slash4you/Anemometre-Girouette/images/Anemometre Electronic v15.png

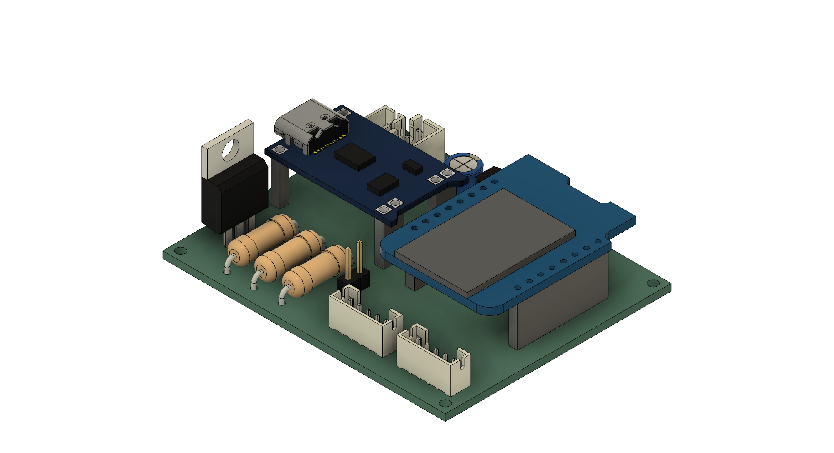
images/Anemometre Electronic v15.png
