slash4you/Anemometre-Girouette/images/Anemometre+Girouette v337.png

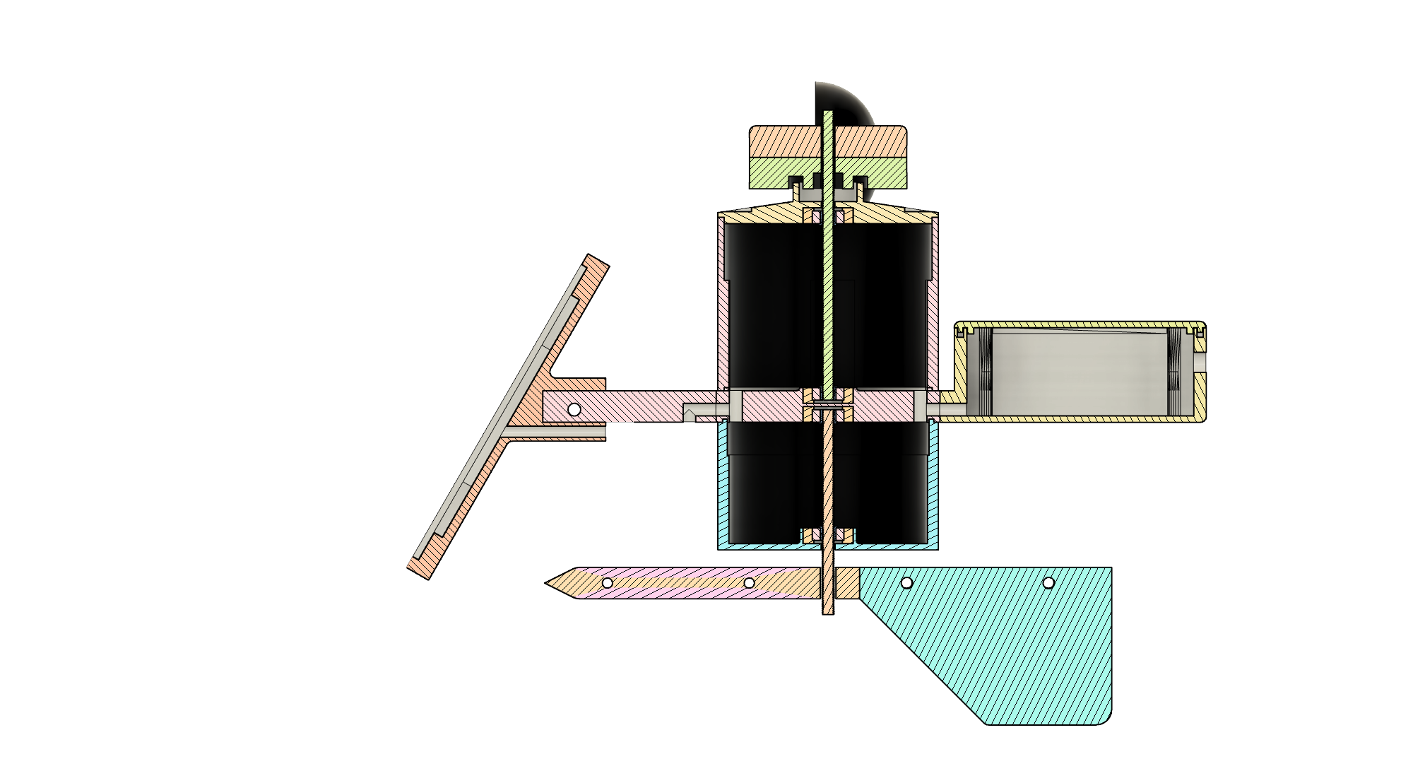
images/Anemometre+Girouette v337.png
