slash4you/Anemometre-Girouette/images/Anemometre+Girouette v337_2.png

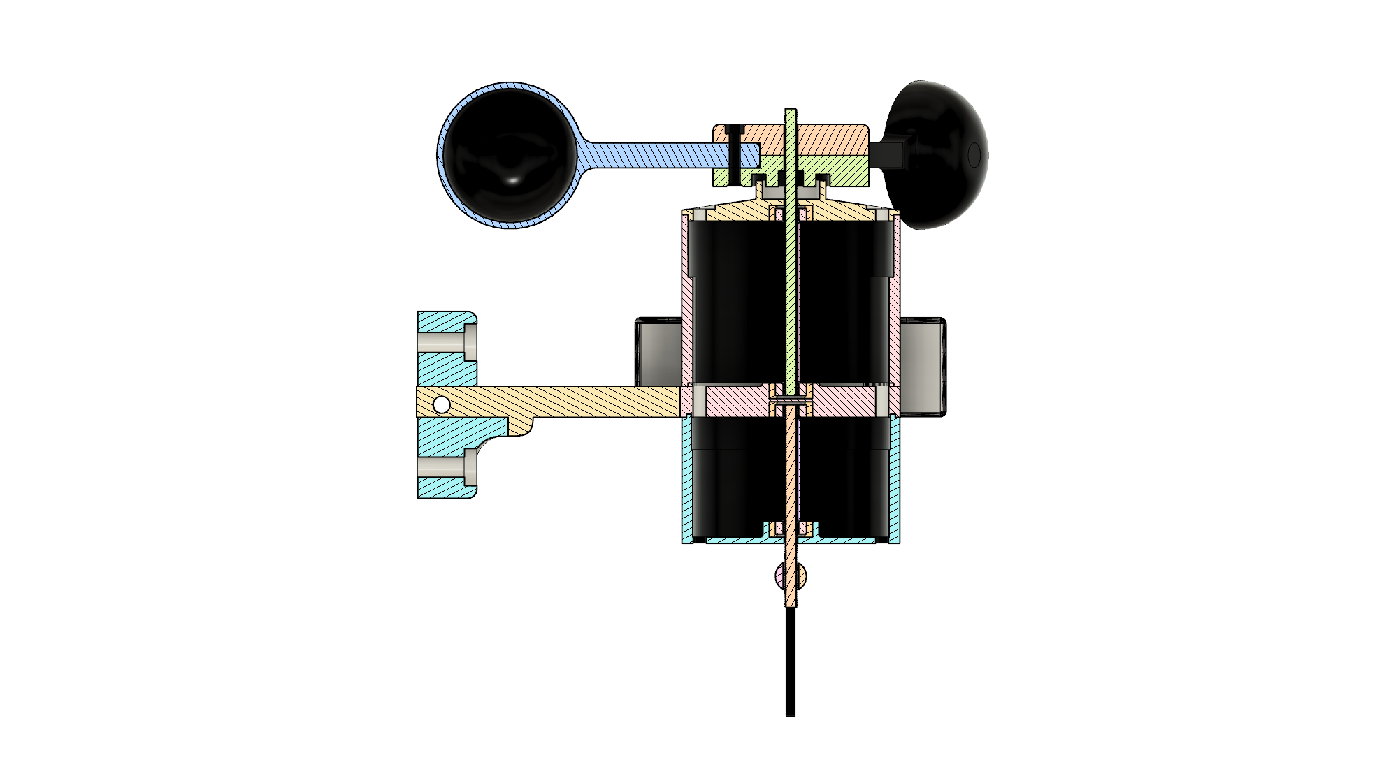
images/Anemometre+Girouette v337_2.png
