slash4you/Anemometre-Girouette/images/Anemometre+Girouette v337_3.png

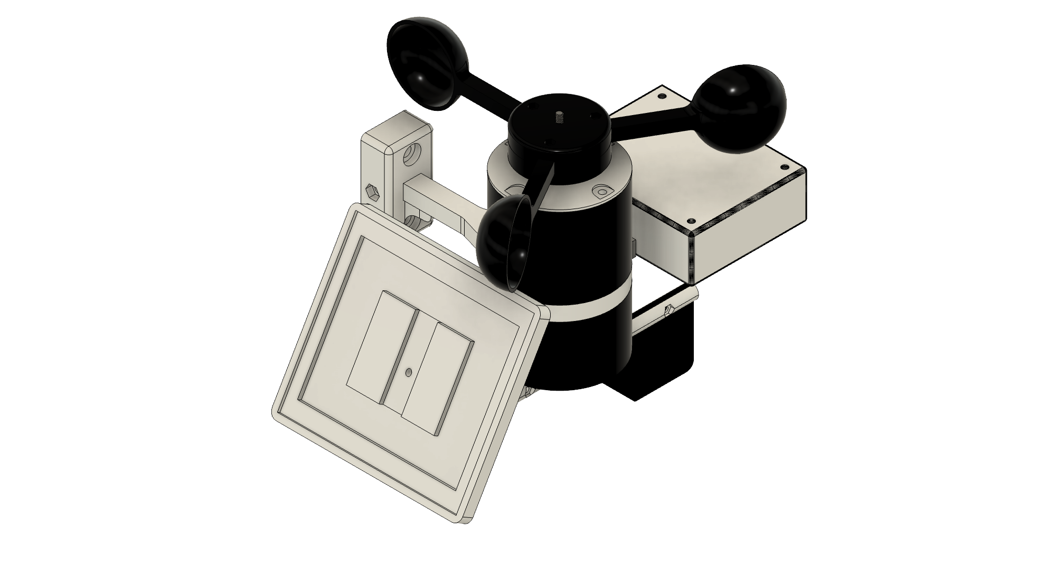
images/Anemometre+Girouette v337_3.png
