slash4you/Anemometre-Girouette/images/Anemometre+Girouette v337_4.png

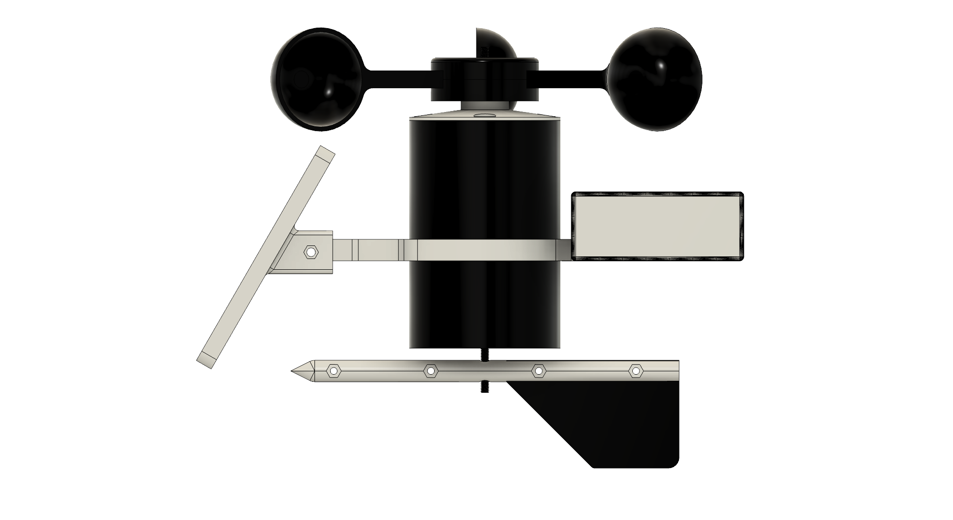
images/Anemometre+Girouette v337_4.png
