slash4you/Anemometre-Girouette/images/Anemometre+Girouette v337_5.png

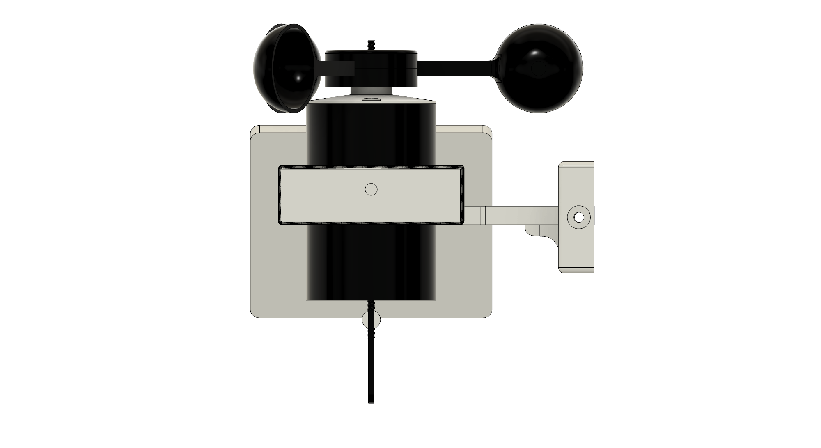
images/Anemometre+Girouette v337_5.png
