slash4you/Anemometre-Girouette/images/Anemometre+Girouette v337_6.png

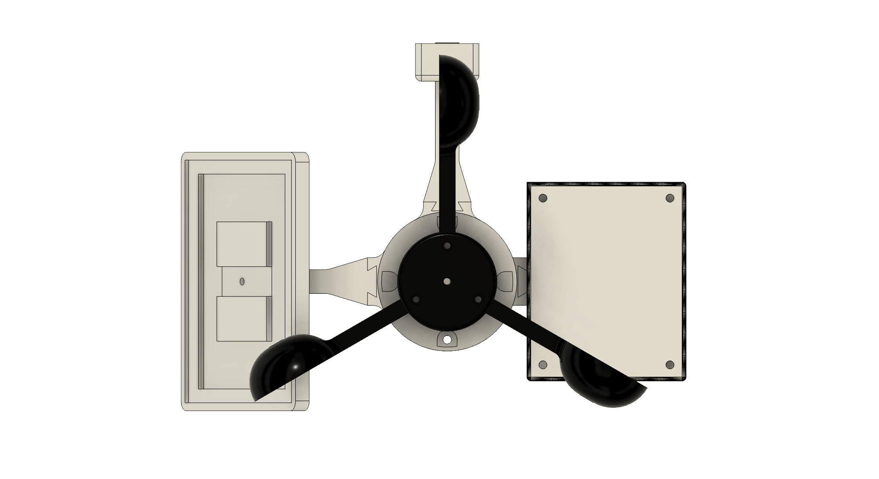
images/Anemometre+Girouette v337_6.png
