slash4you/Anemometre-Girouette/images/Anemometre+Girouette v343.png

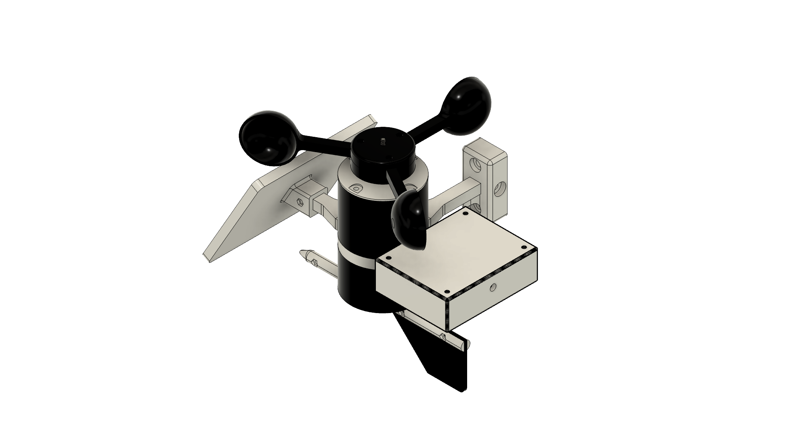
images/Anemometre+Girouette v343.png
