slash4you/Anemometre-Girouette/images/Anemometre+Girouette v345.png

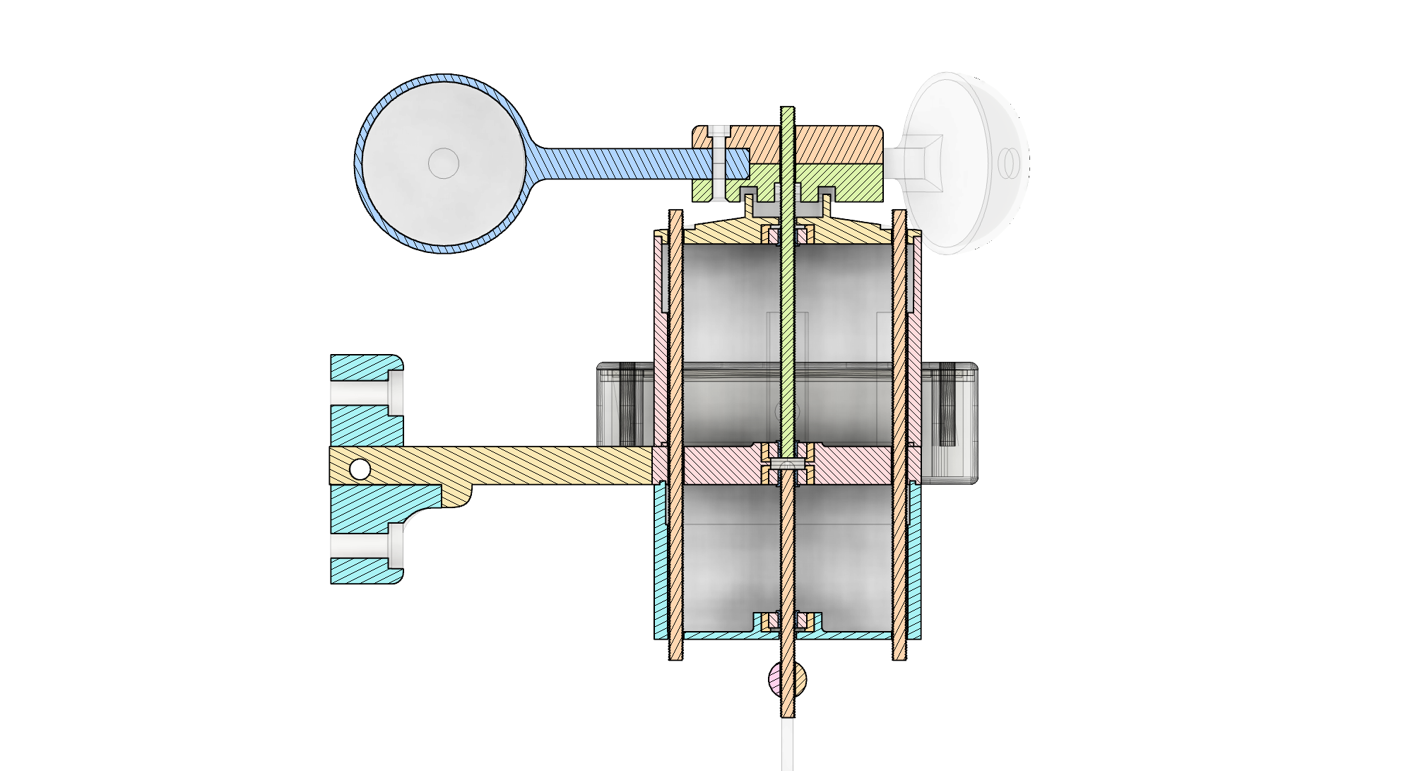
images/Anemometre+Girouette v345.png
