slash4you/Anemometre-Girouette/images/Anemometre+Girouette v345_2.png

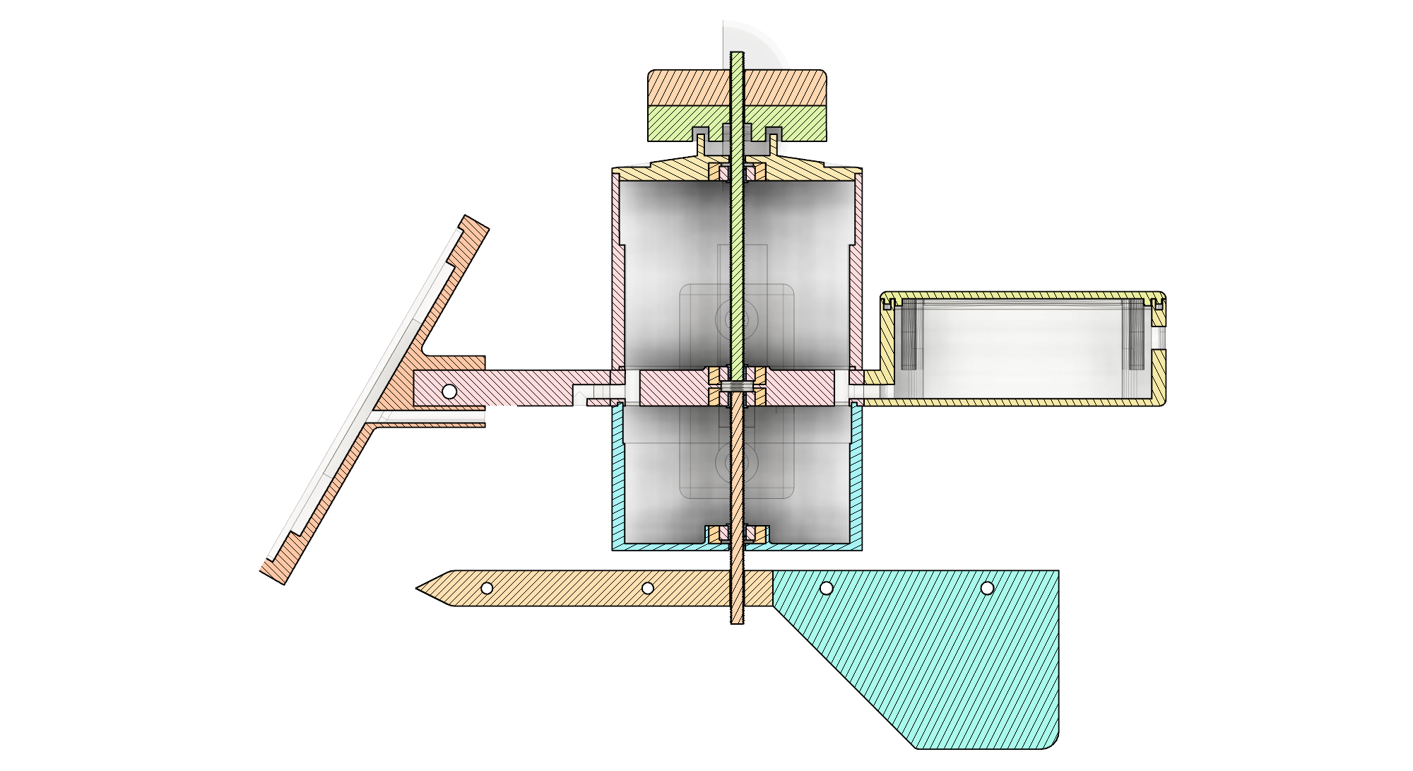
images/Anemometre+Girouette v345_2.png
