slash4you/Anemometre-Girouette/images/Anemometre+Girouette v345_3.png

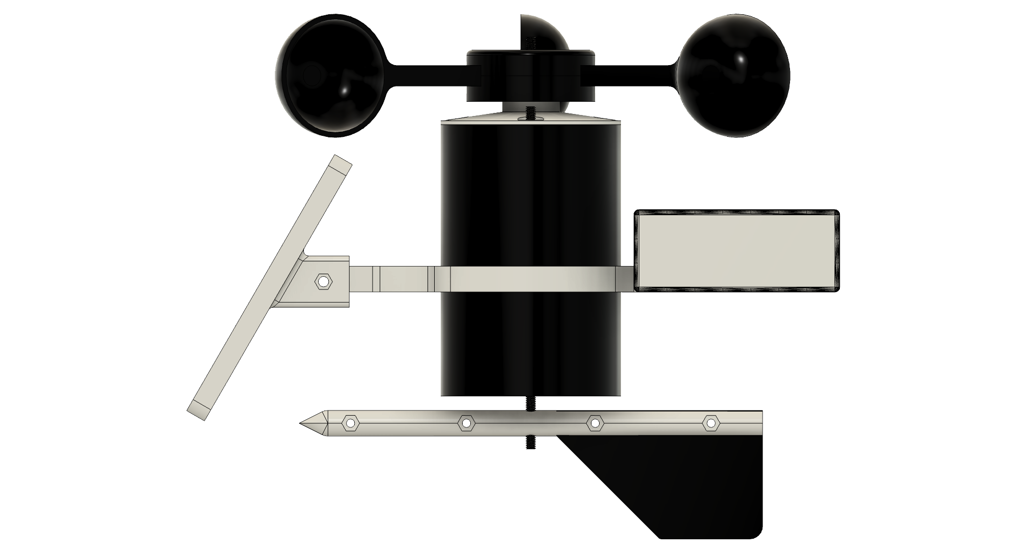
images/Anemometre+Girouette v345_3.png
