slash4you/Anemometre-Girouette/images/Anemometre+Girouette v345_5.png

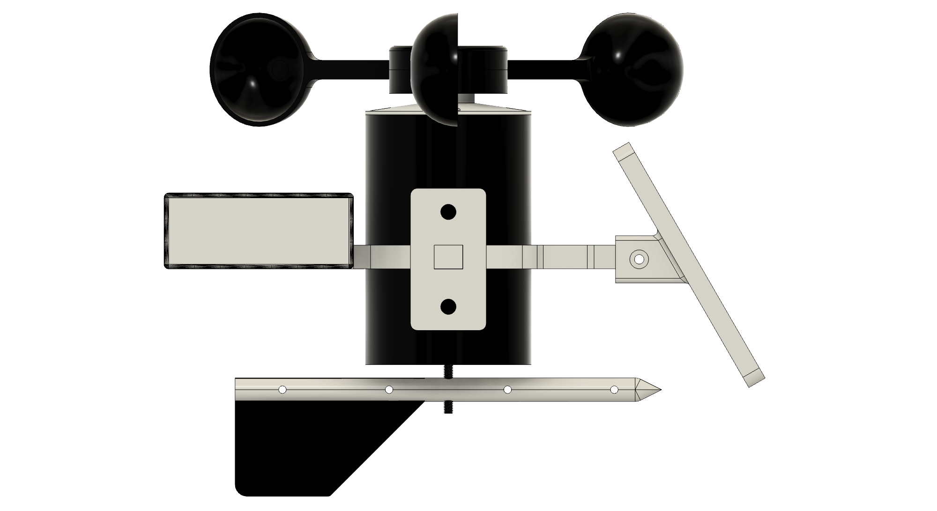
images/Anemometre+Girouette v345_5.png
