slash4you/Anemometre-Girouette/images/Anemometre+Girouette v345_6.png

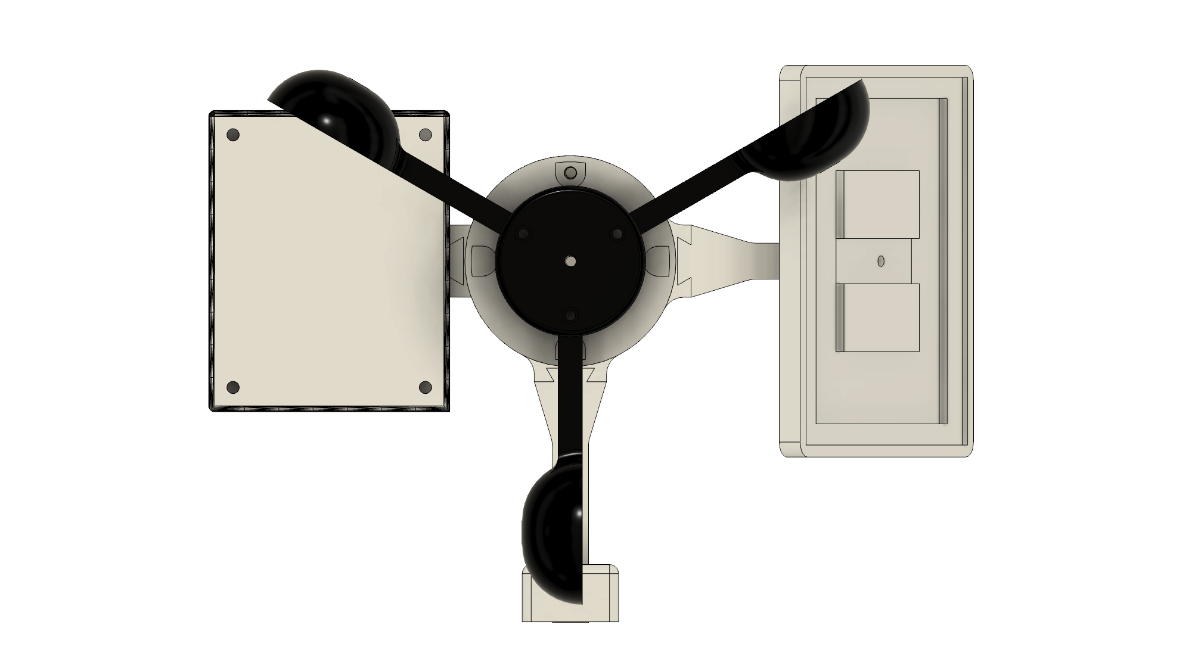
images/Anemometre+Girouette v345_6.png
