slash4you/Anemometre-Girouette/images/Anemometre+Girouette v345_7.png

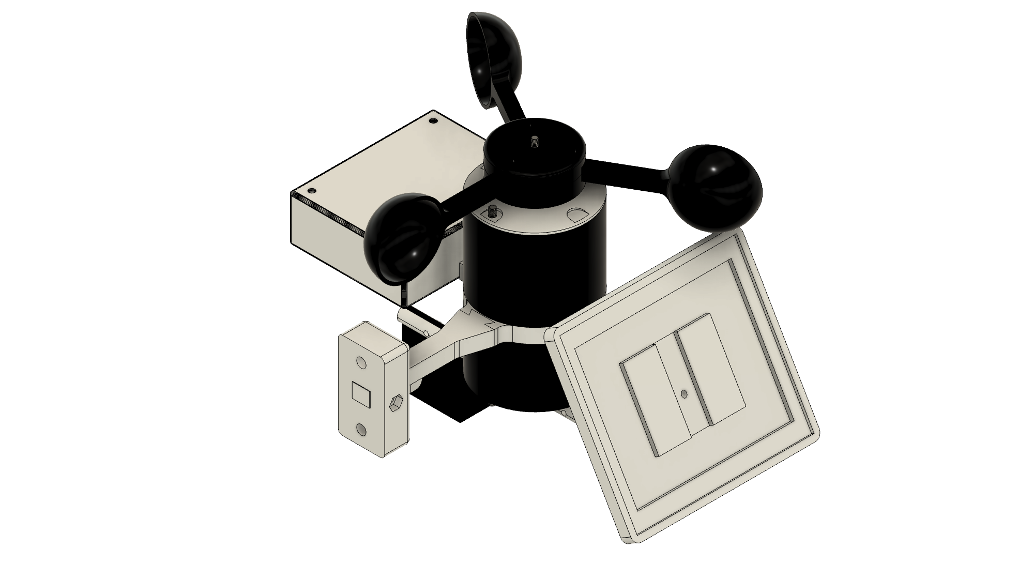
images/Anemometre+Girouette v345_7.png
