slash4you/Anemometre-Girouette/images/Anemometre+Girouette v345_8.png

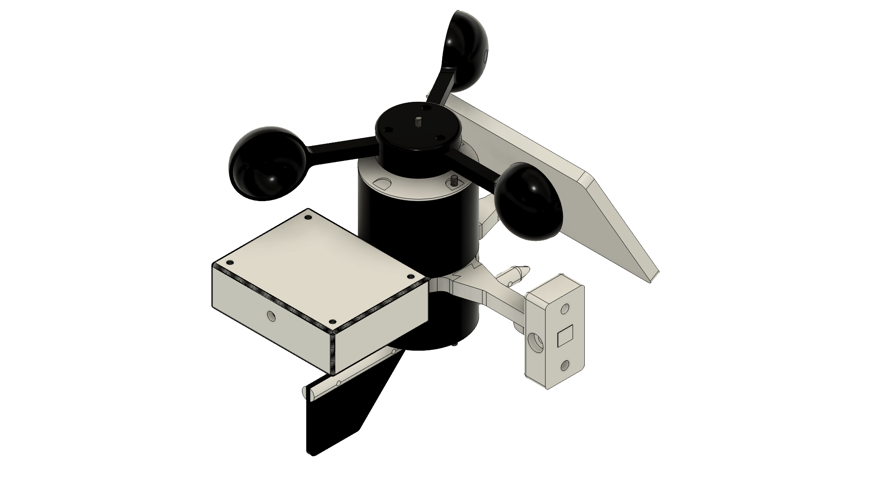
images/Anemometre+Girouette v345_8.png
