slash4you/Anemometre-Girouette/images/Anemometre+Girouette v345_10.png

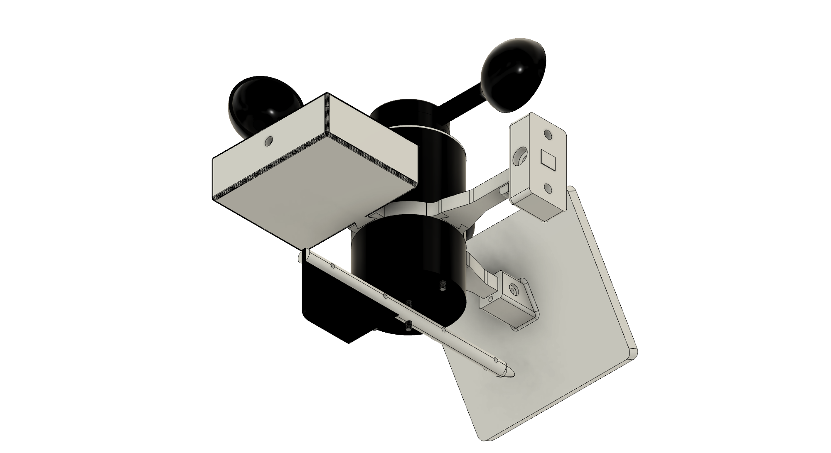
images/Anemometre+Girouette v345_10.png
