slash4you/Anemometre-Girouette/images/Anemometre+Girouette v364.png

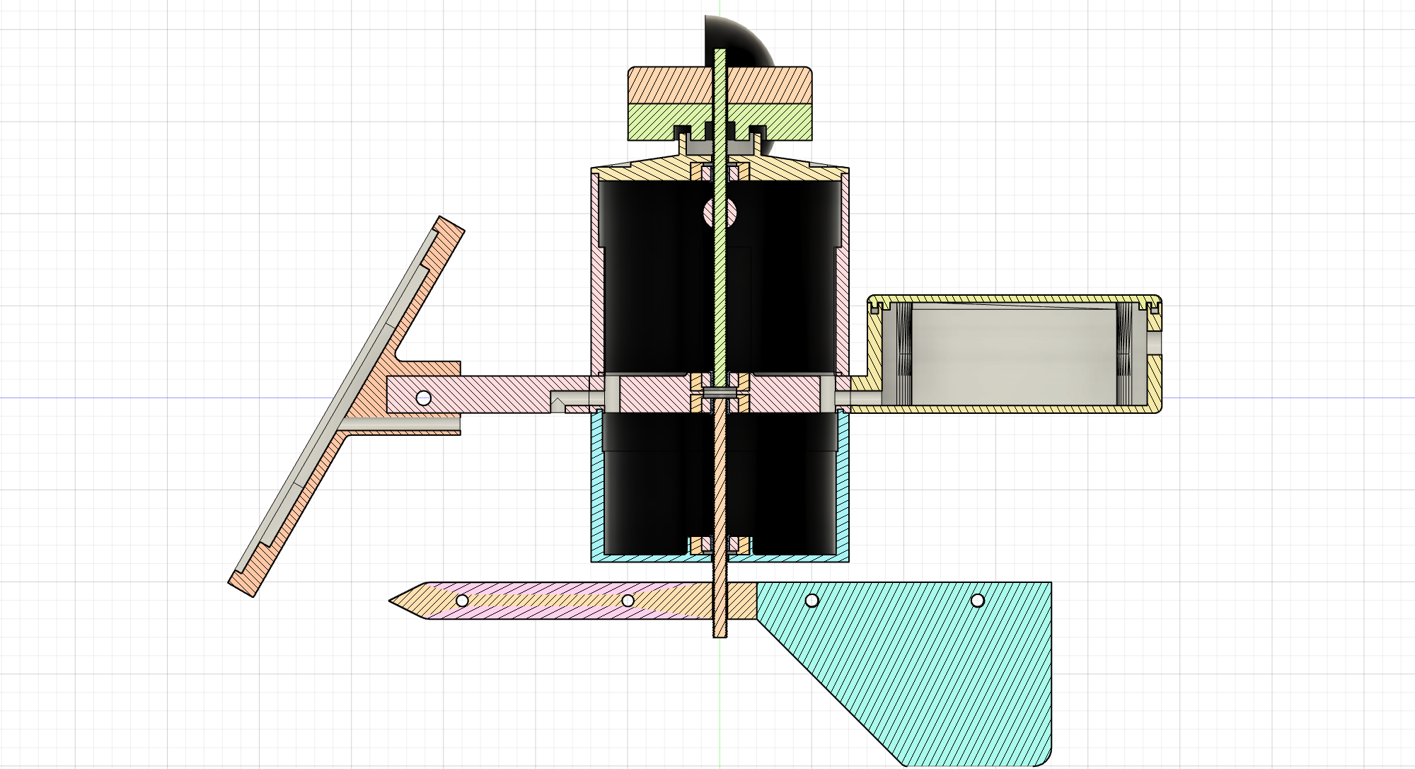
images/Anemometre+Girouette v364.png
