slash4you/Anemometre-Girouette/images/Anemometre+Girouette v364_2.png

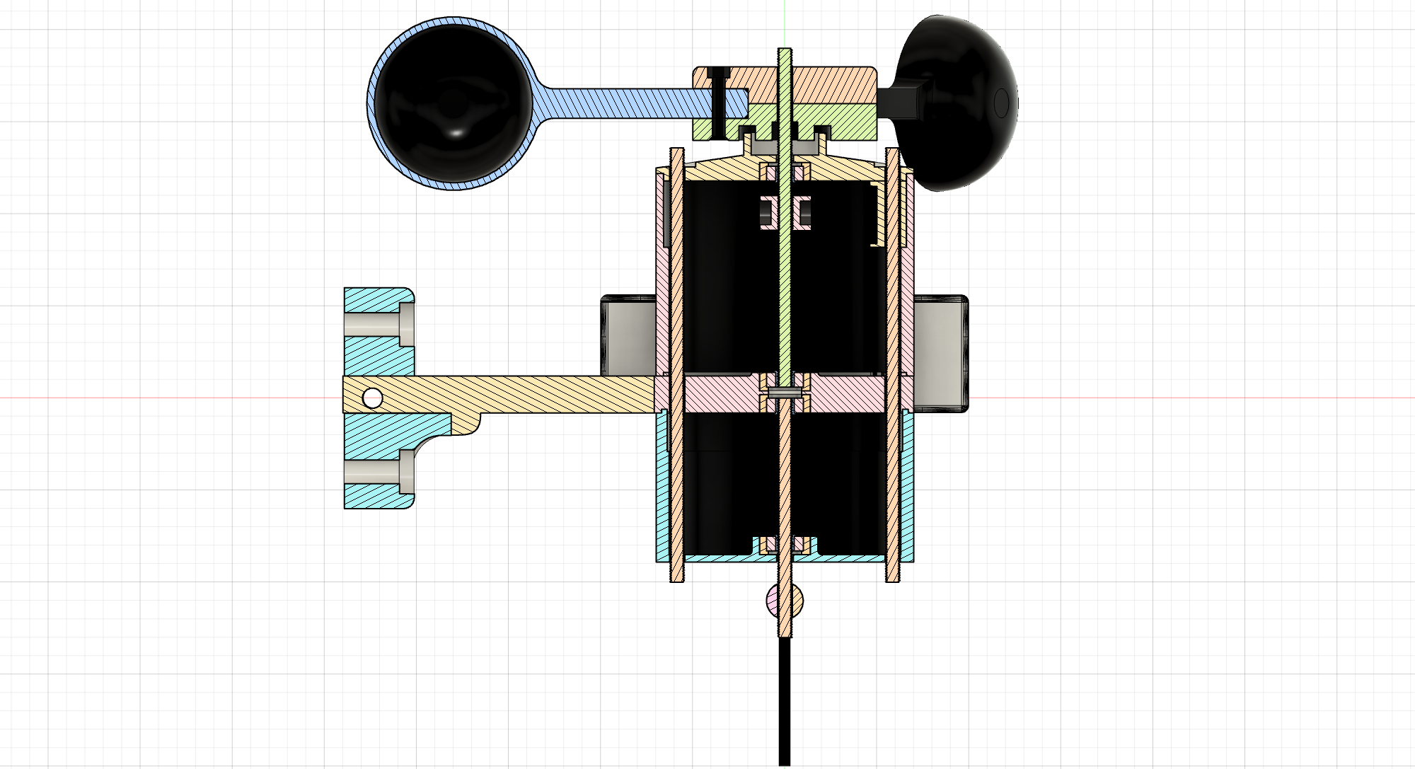
images/Anemometre+Girouette v364_2.png
