slash4you/Anemometre-Girouette/images/Anemometre+Girouette v364_3.png

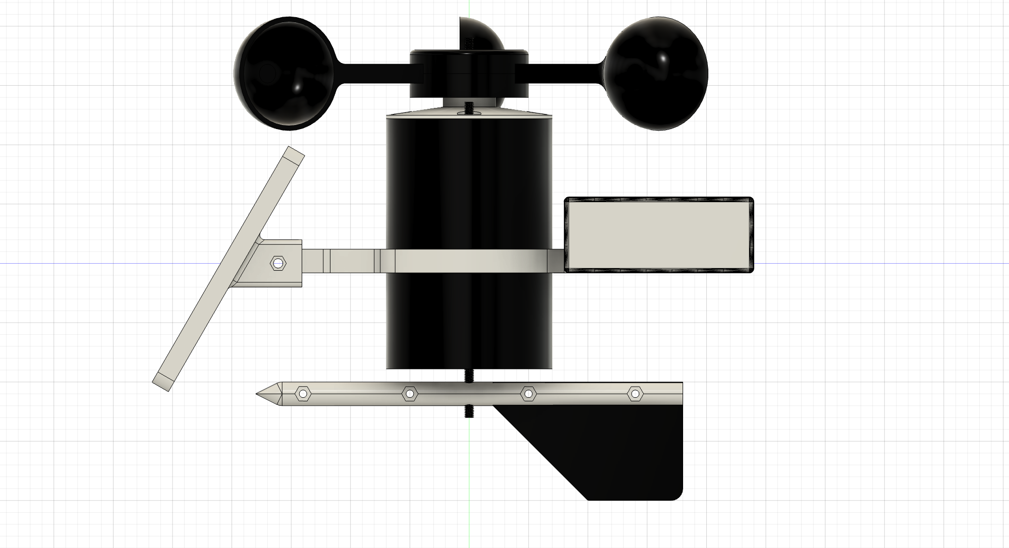
images/Anemometre+Girouette v364_3.png
