slash4you/Anemometre-Girouette/images/Anemometre+Girouette v364_4.png

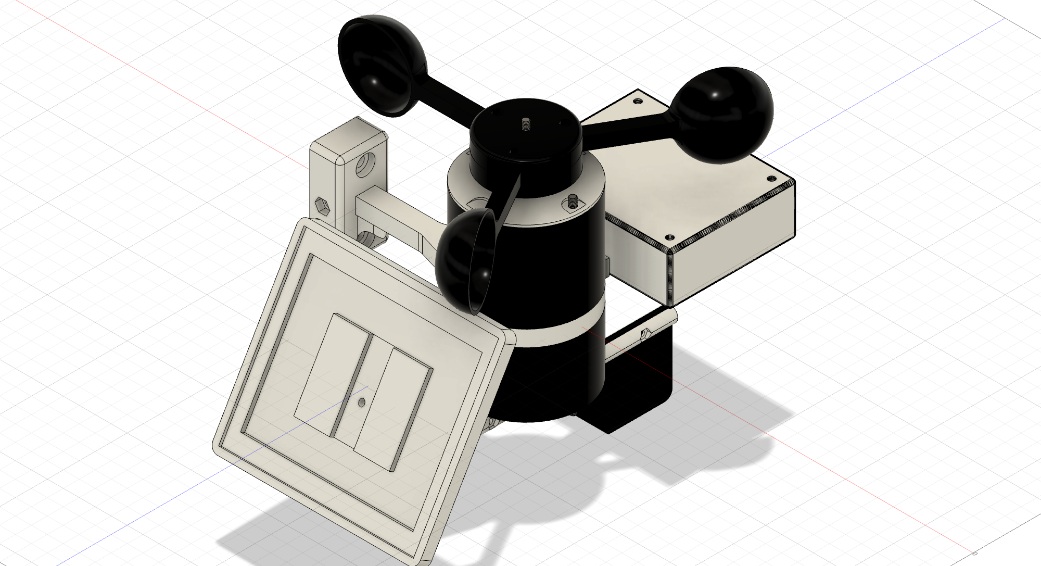
images/Anemometre+Girouette v364_4.png
