slash4you/Anemometre-Girouette/images/Anemometre+Girouette v364_5.png

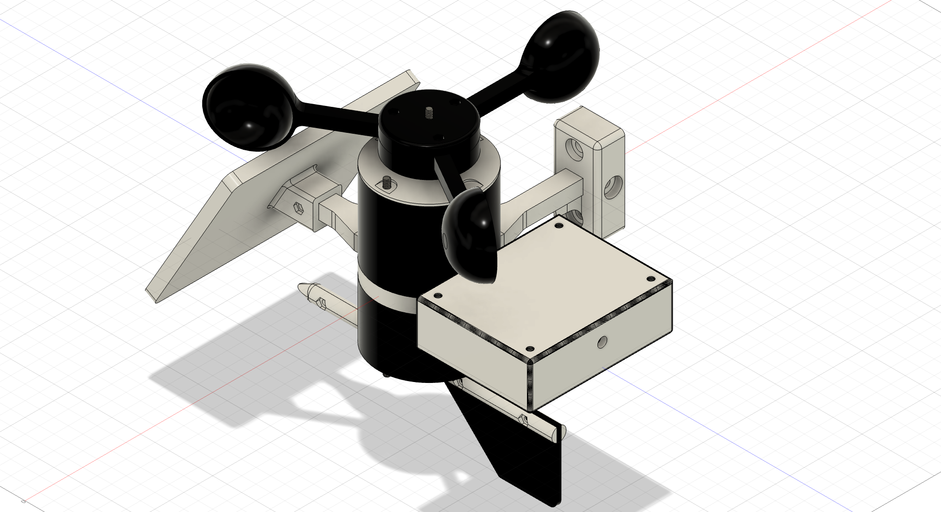
images/Anemometre+Girouette v364_5.png
