slash4you/Anemometre-Girouette/images/Anemometre+Girouette v364_6.png

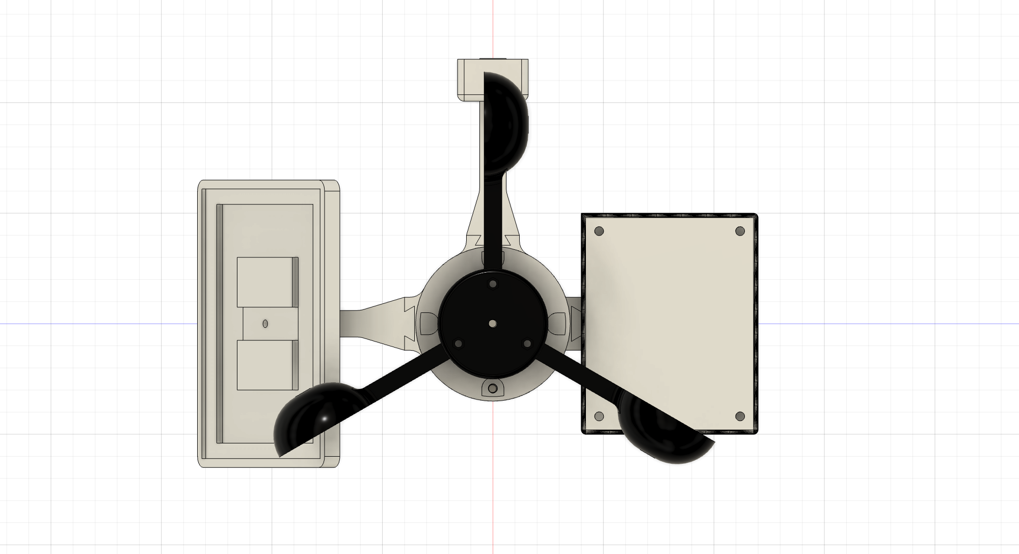
images/Anemometre+Girouette v364_6.png
