slash4you/Anemometre-Girouette/images/Anemometre+Girouette v364_7.png

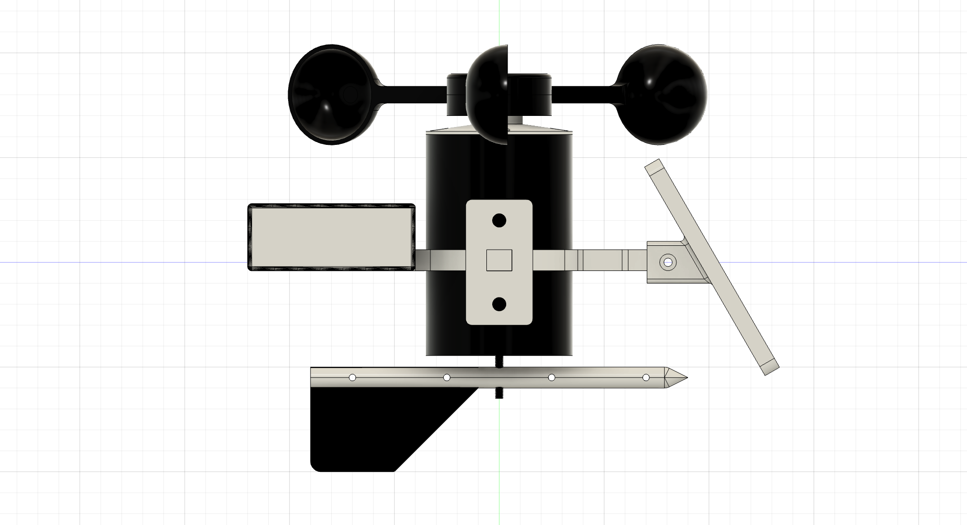
images/Anemometre+Girouette v364_7.png
