slash4you/Anemometre-Girouette/images/Anemometre+Girouette v364_8.png

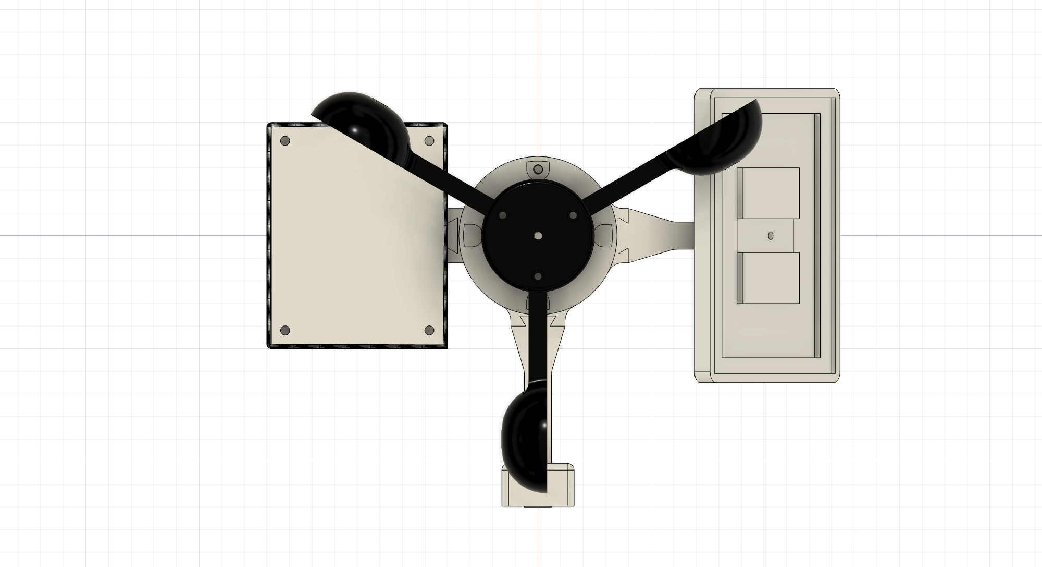
images/Anemometre+Girouette v364_8.png
