slash4you/Anemometre-Girouette/images/Anemometre+Girouette v364_9.png

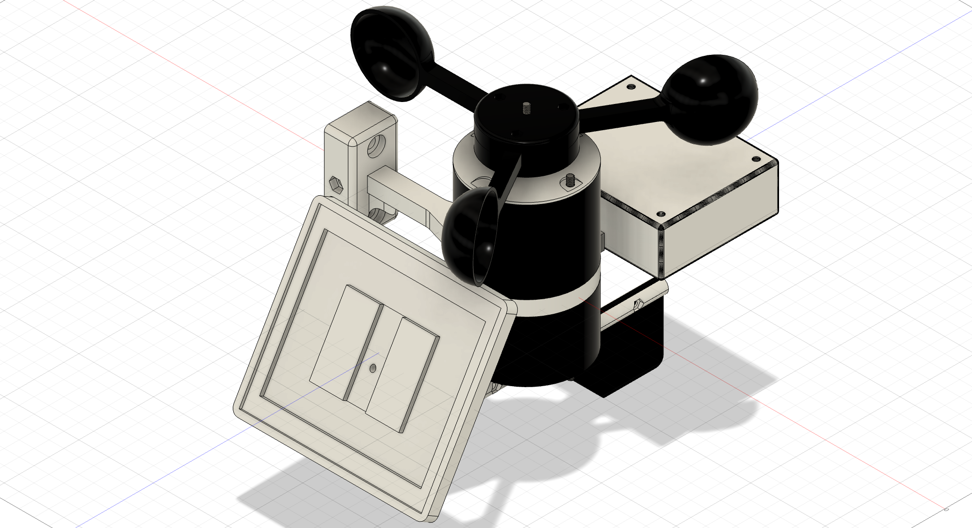
images/Anemometre+Girouette v364_9.png
