slash4you/Anemometre-Girouette/images/Anemometre+Girouette v372.png

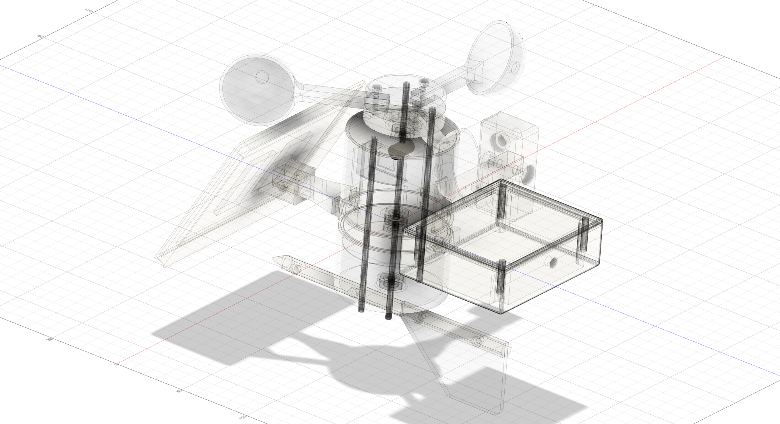
images/Anemometre+Girouette v372.png
