slash4you/Anemometre-Girouette/images/Anemometre+Girouette v388.png

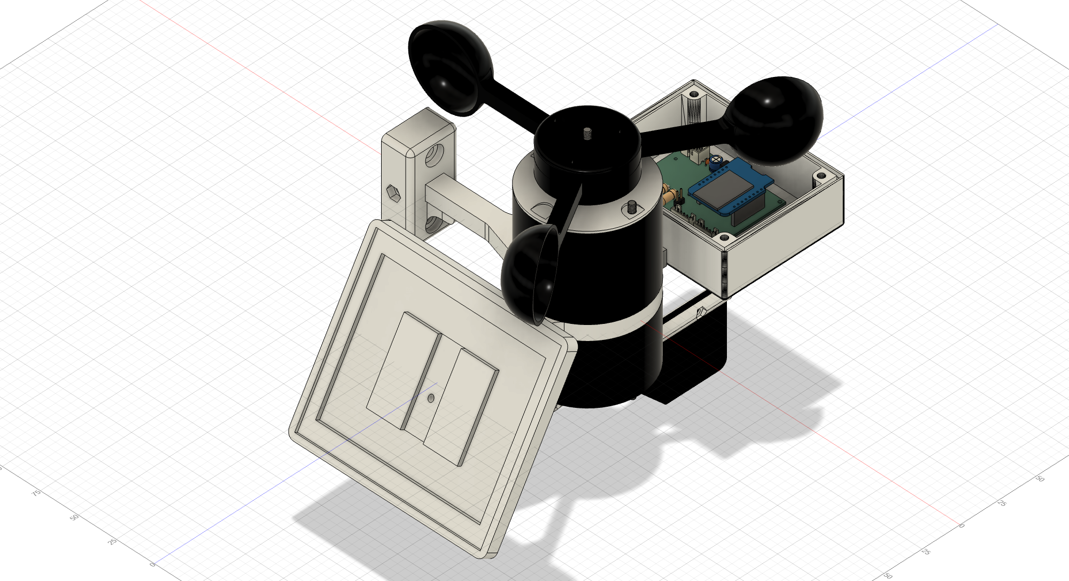
images/Anemometre+Girouette v388.png
