slash4you/Anemometre-Girouette/images/Anemometre+Girouette v388_2.png

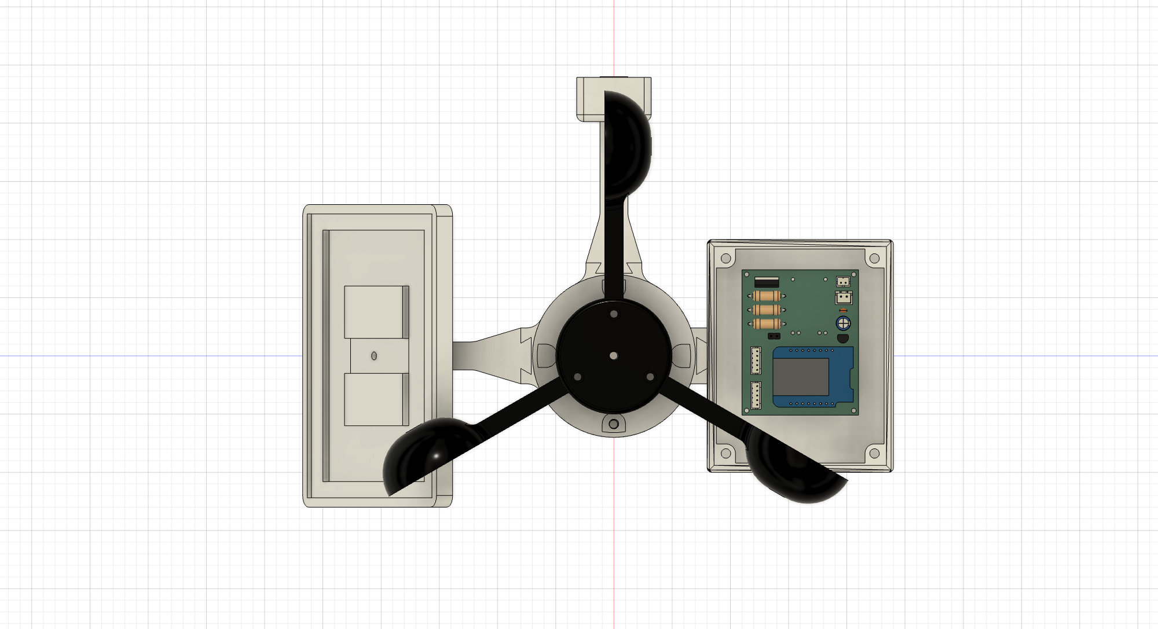
images/Anemometre+Girouette v388_2.png
