slash4you/Anemometre-Girouette/images/Anemometre+Girouette v388_3.png

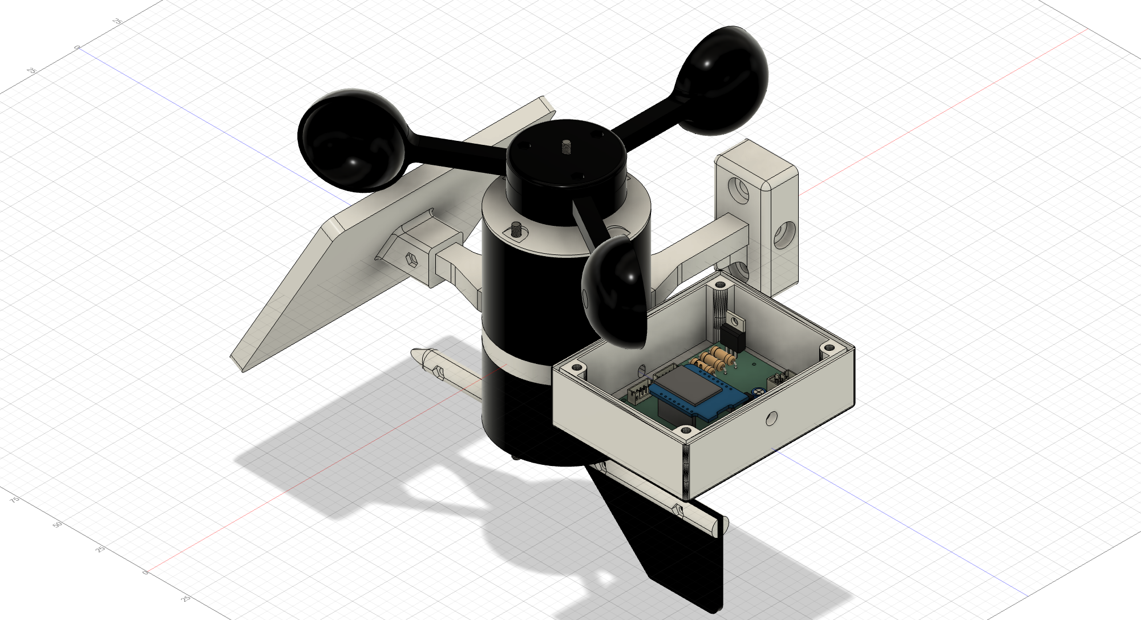
images/Anemometre+Girouette v388_3.png
