slash4you/Anemometre-Girouette/images/Anemometre+Girouette v388_4.png

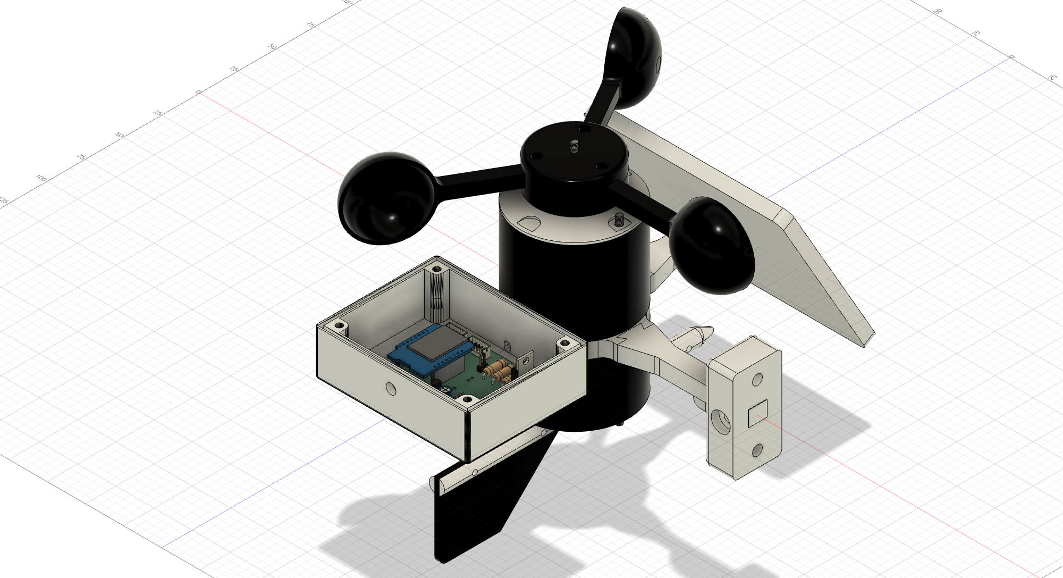
images/Anemometre+Girouette v388_4.png
