slash4you/Anemometre-Girouette/images/Anemometre+Girouette v390.png

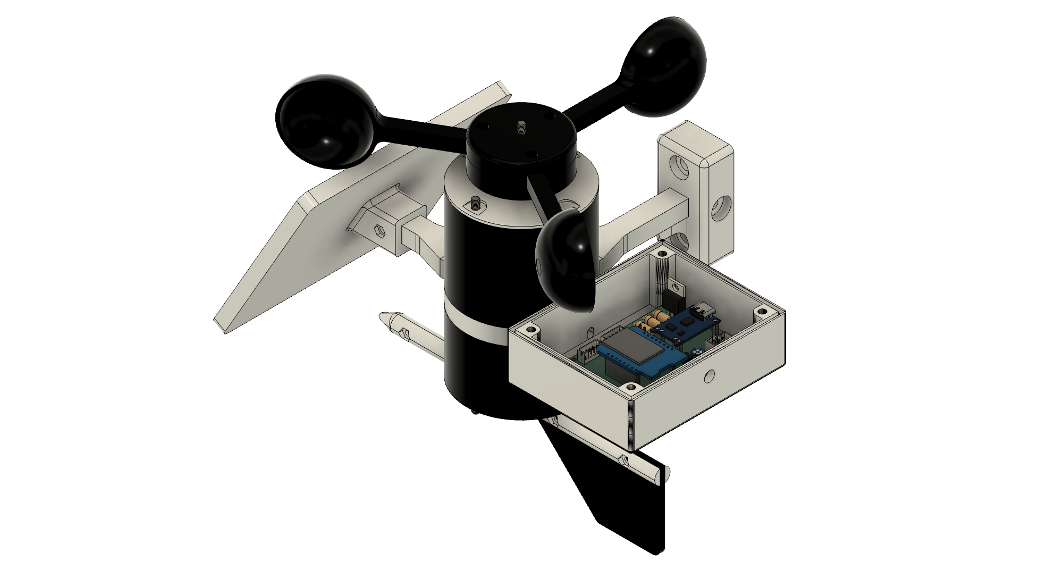
images/Anemometre+Girouette v390.png
