slash4you/Anemometre-Girouette/images/Anemometre+Girouette v390_2.png

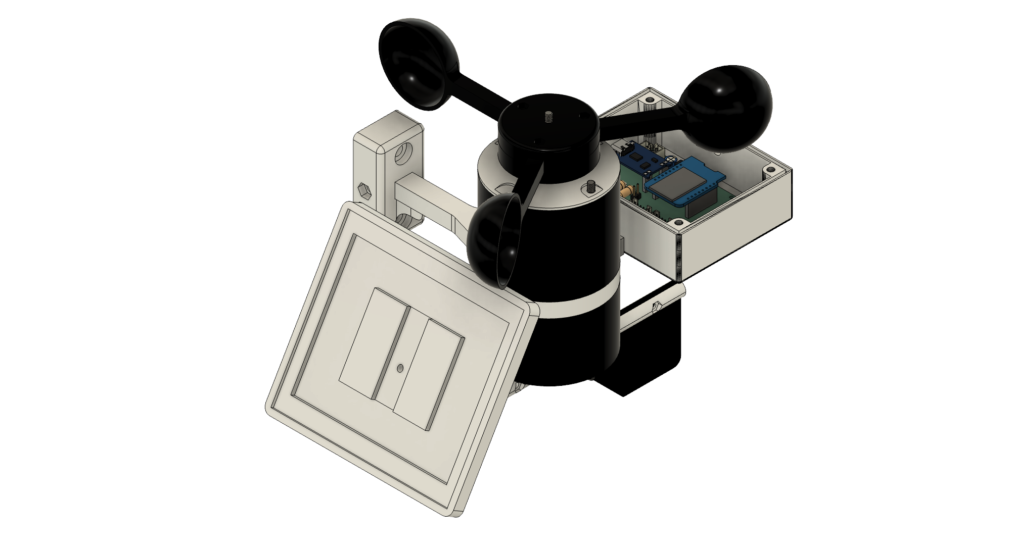
images/Anemometre+Girouette v390_2.png
