slash4you/Anemometre-Girouette/images/Anemometre+Girouette v390_3.png

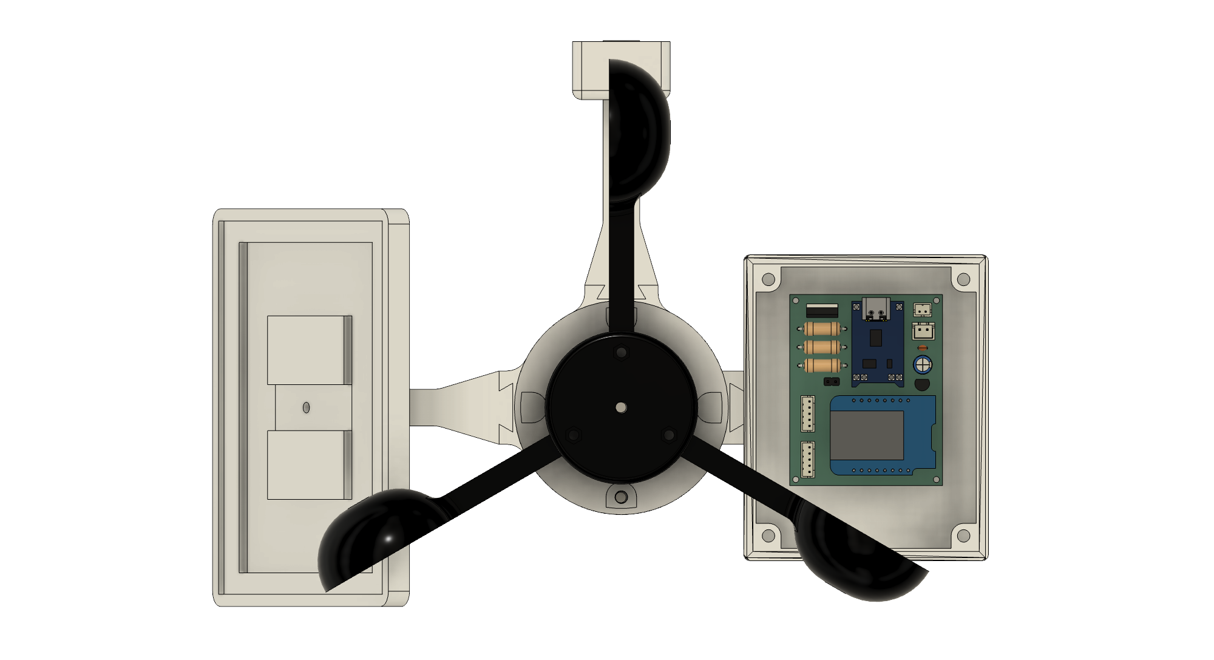
images/Anemometre+Girouette v390_3.png
