slash4you/Anemometre-Girouette/images/Anemometre+Girouette v399_2.png

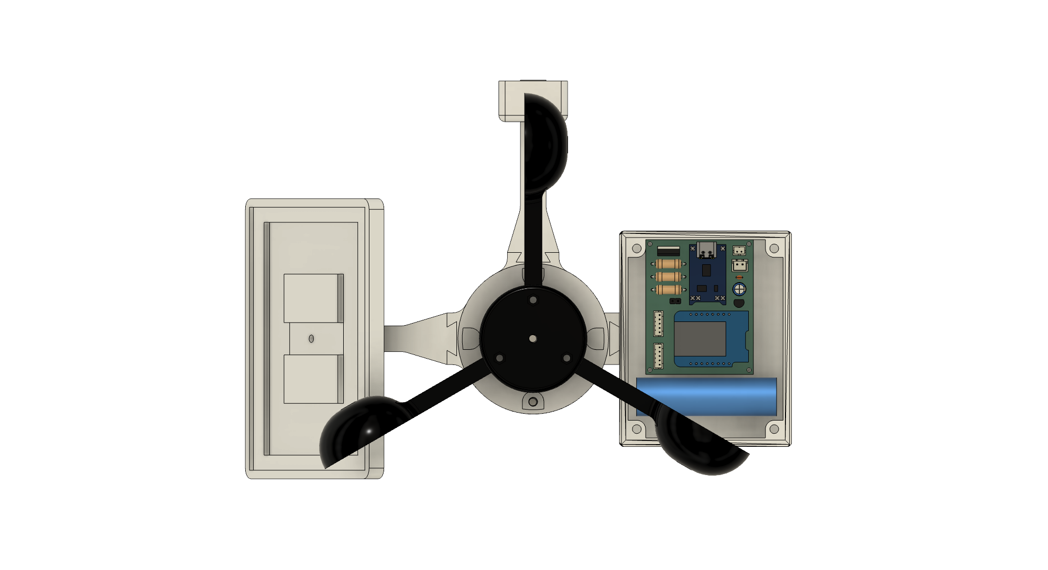
images/Anemometre+Girouette v399_2.png
