slash4you/Anemometre-Girouette/images/Anemometre+Girouette v399_3.png

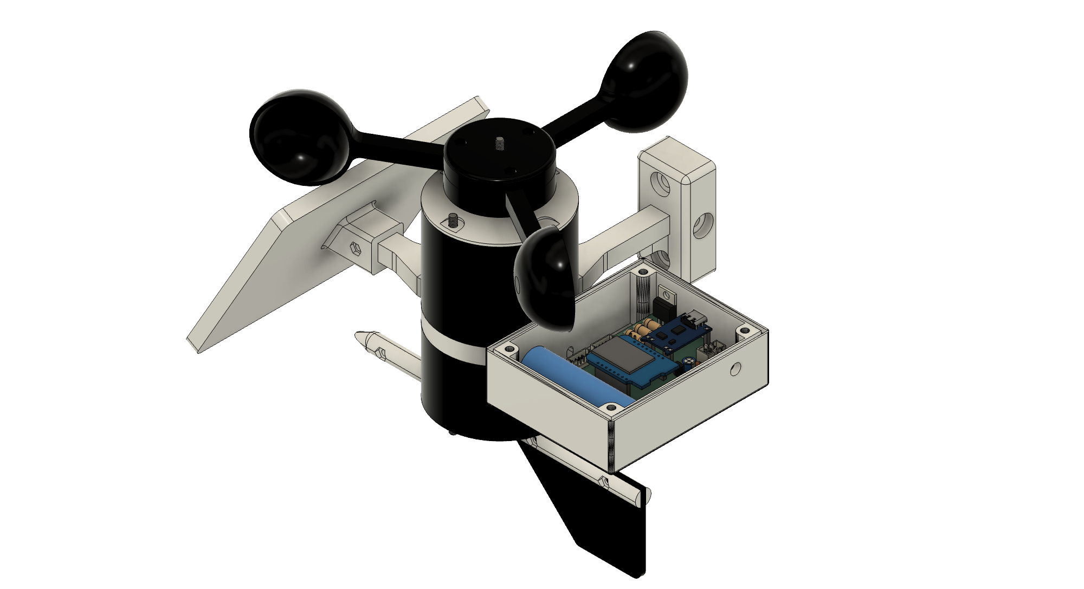
images/Anemometre+Girouette v399_3.png
