slash4you/Anemometre-Girouette/images/Anemometre+Girouette v399_4.png

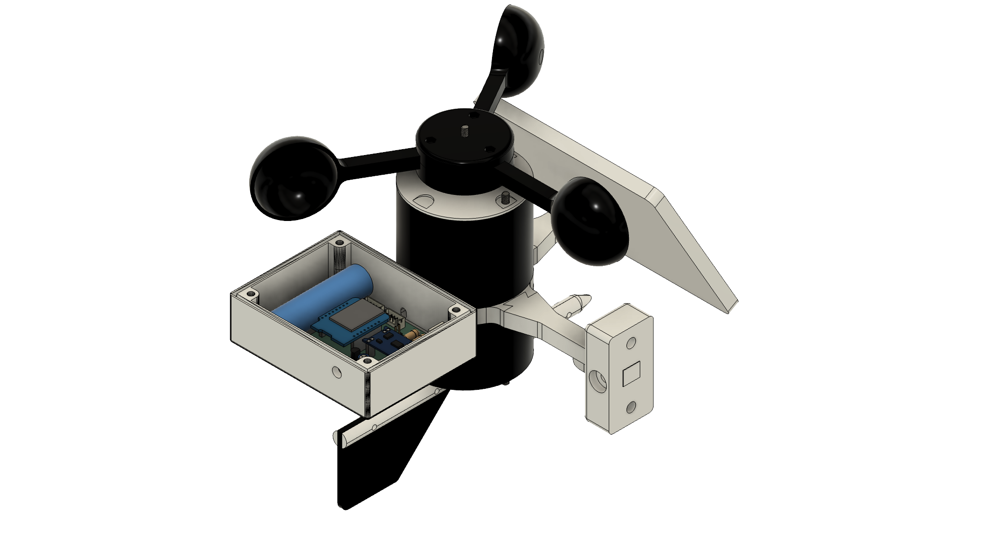
images/Anemometre+Girouette v399_4.png
