slash4you/Anemometre-Girouette/images/Anemometre+Girouette v514.png

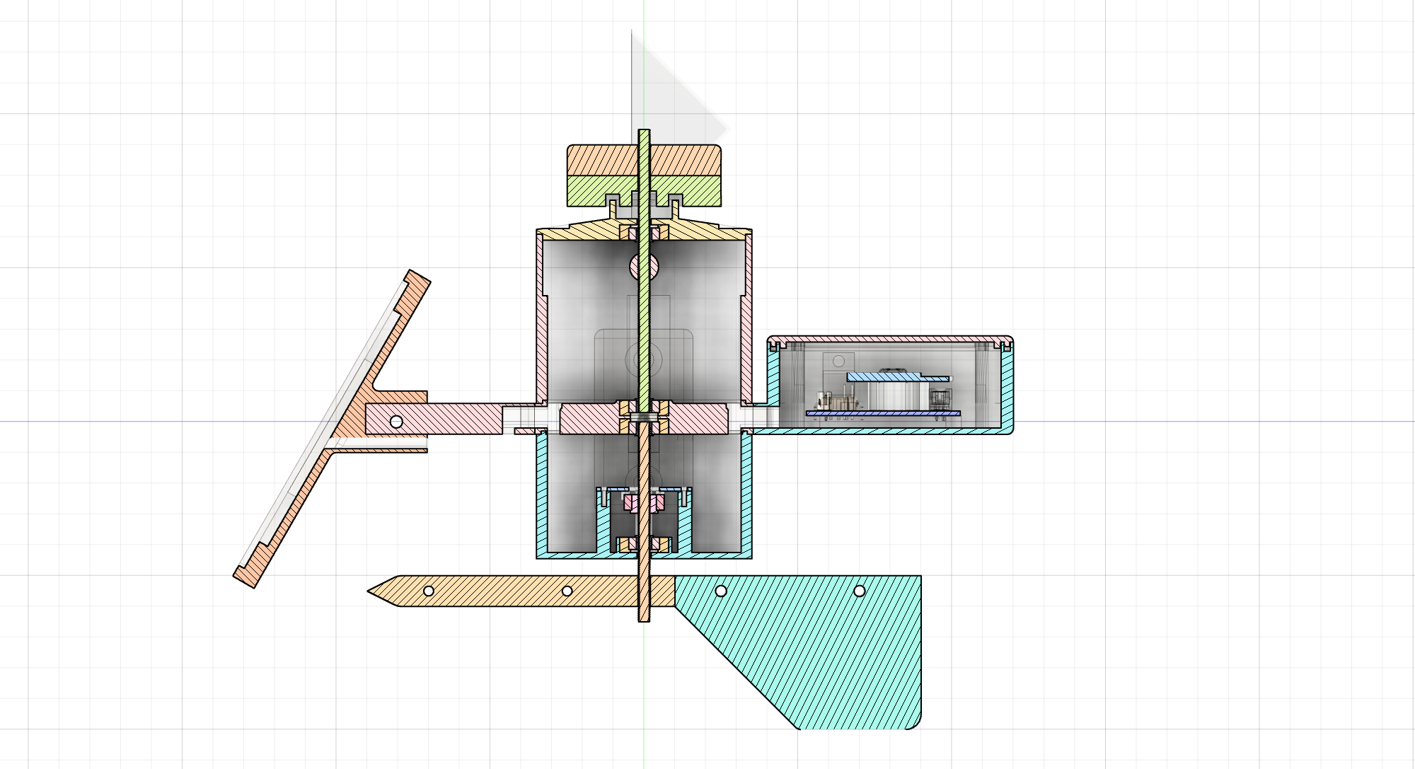
images/Anemometre+Girouette v514.png
