slash4you/Anemometre-Girouette/images/Anemometre+Girouette v514_2.png

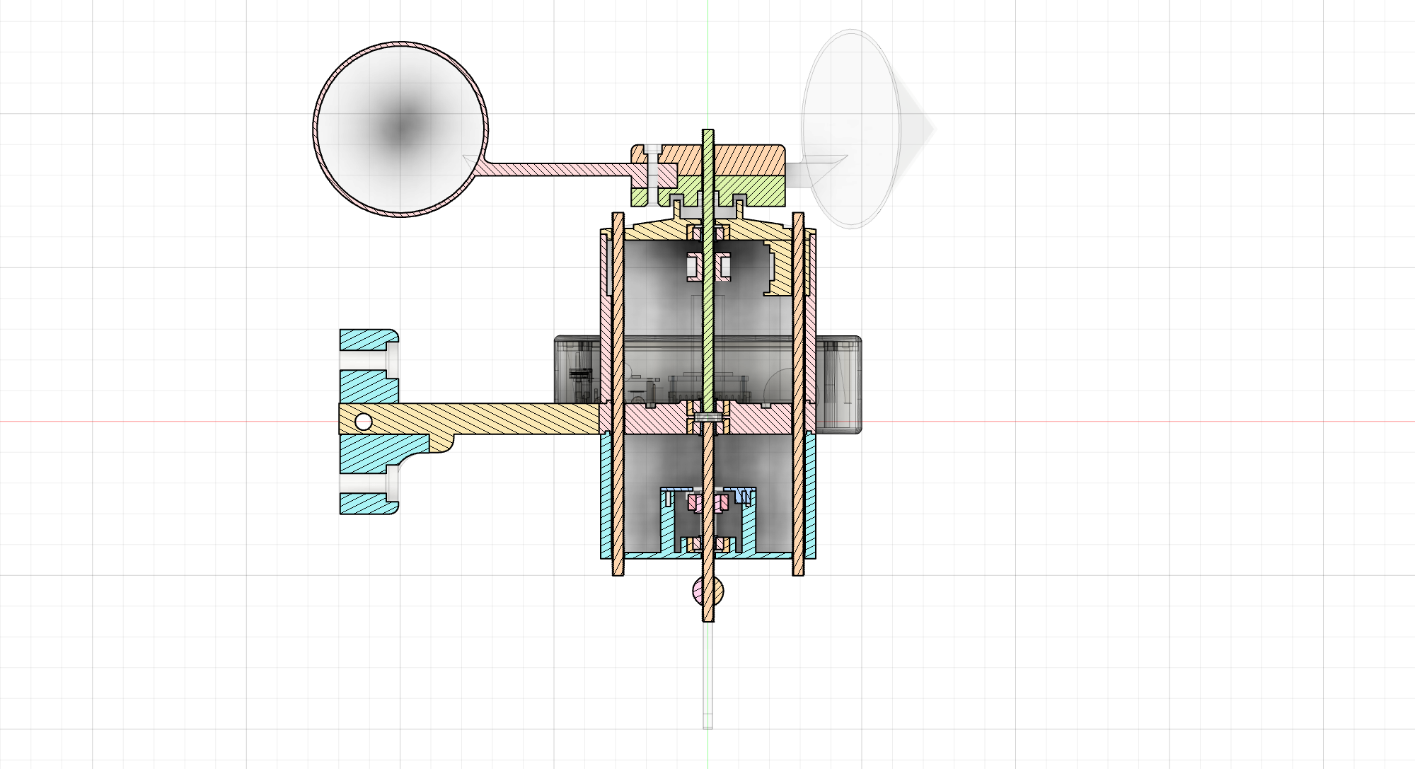
images/Anemometre+Girouette v514_2.png
