slash4you/Anemometre-Girouette/images/Anemometre+Girouette v514_3.png

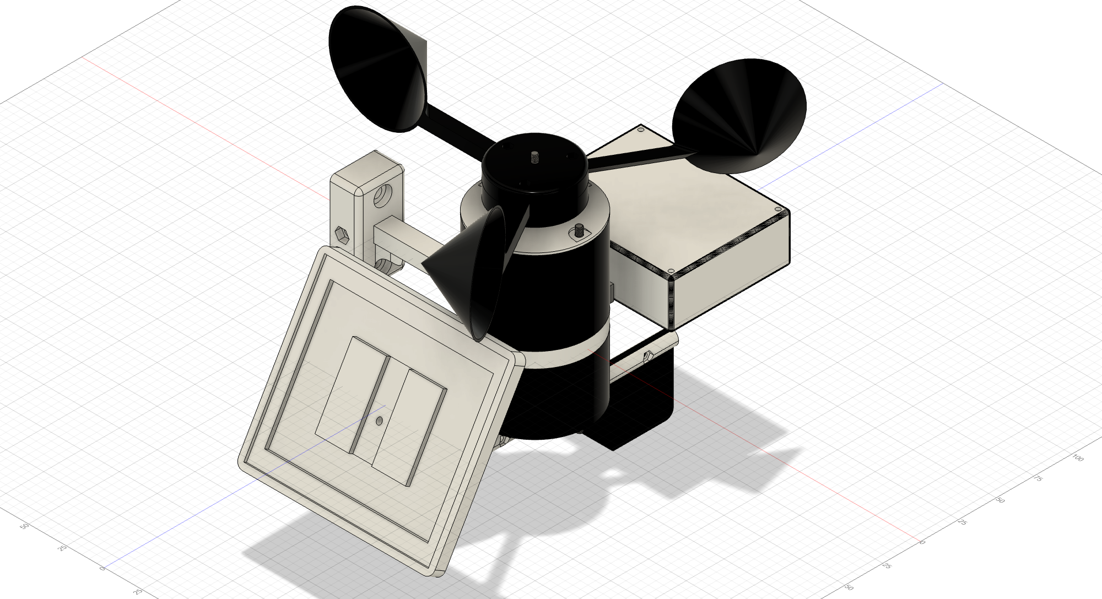
images/Anemometre+Girouette v514_3.png
