slash4you/Anemometre-Girouette/images/Anemometre+Girouette v514_4.png

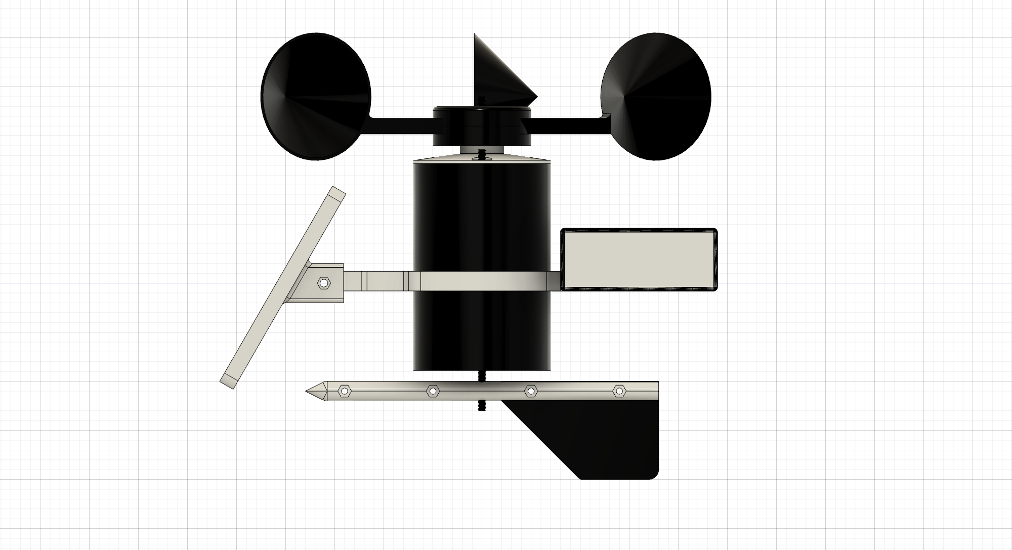
images/Anemometre+Girouette v514_4.png
