slash4you/Anemometre-Girouette/images/Anemometre+Girouette v514_7.png

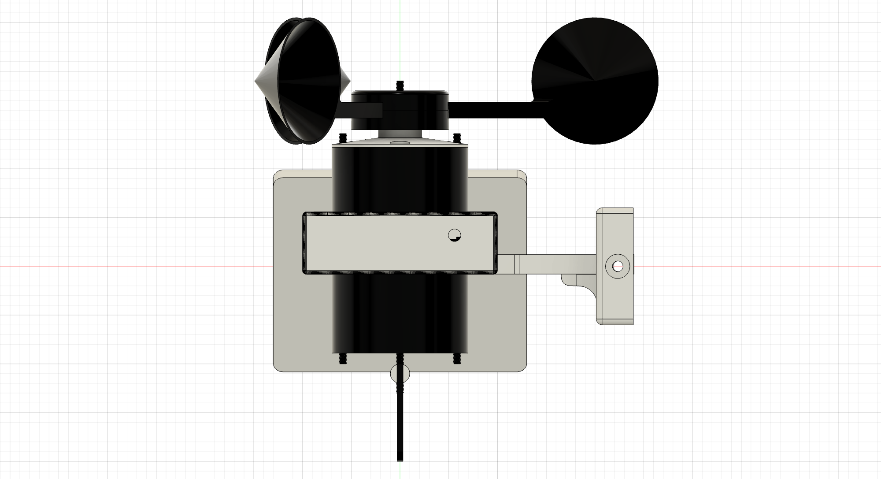
images/Anemometre+Girouette v514_7.png
