slash4you/Anemometre-Girouette/images/Anemometre+Girouette v514_8.png

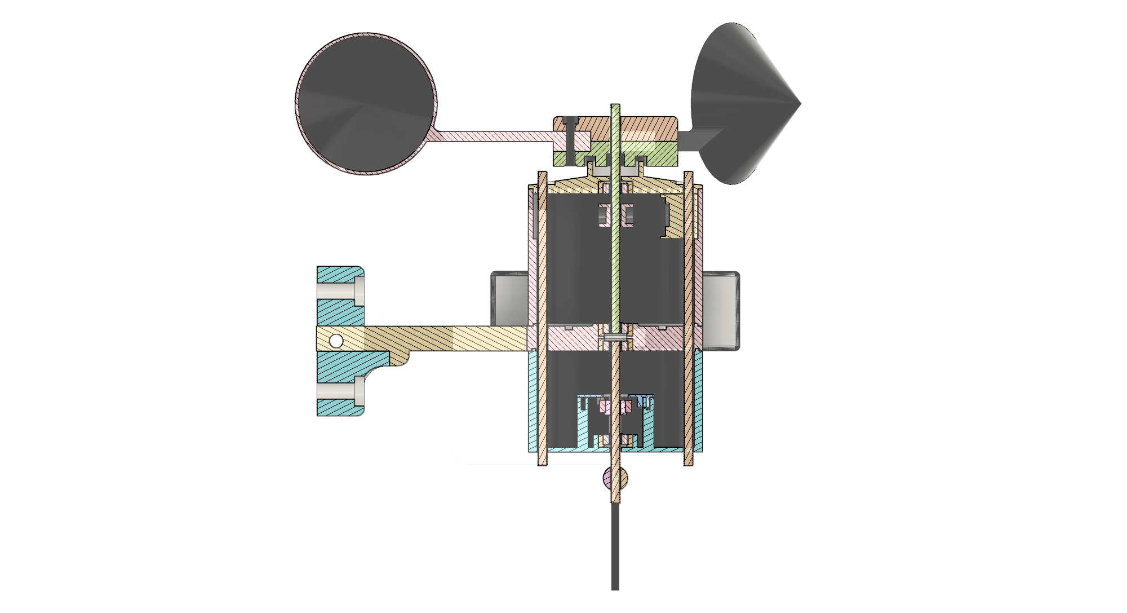
images/Anemometre+Girouette v514_8.png
