slash4you/Anemometre-Girouette/images/Anemometre+Girouette v535.png

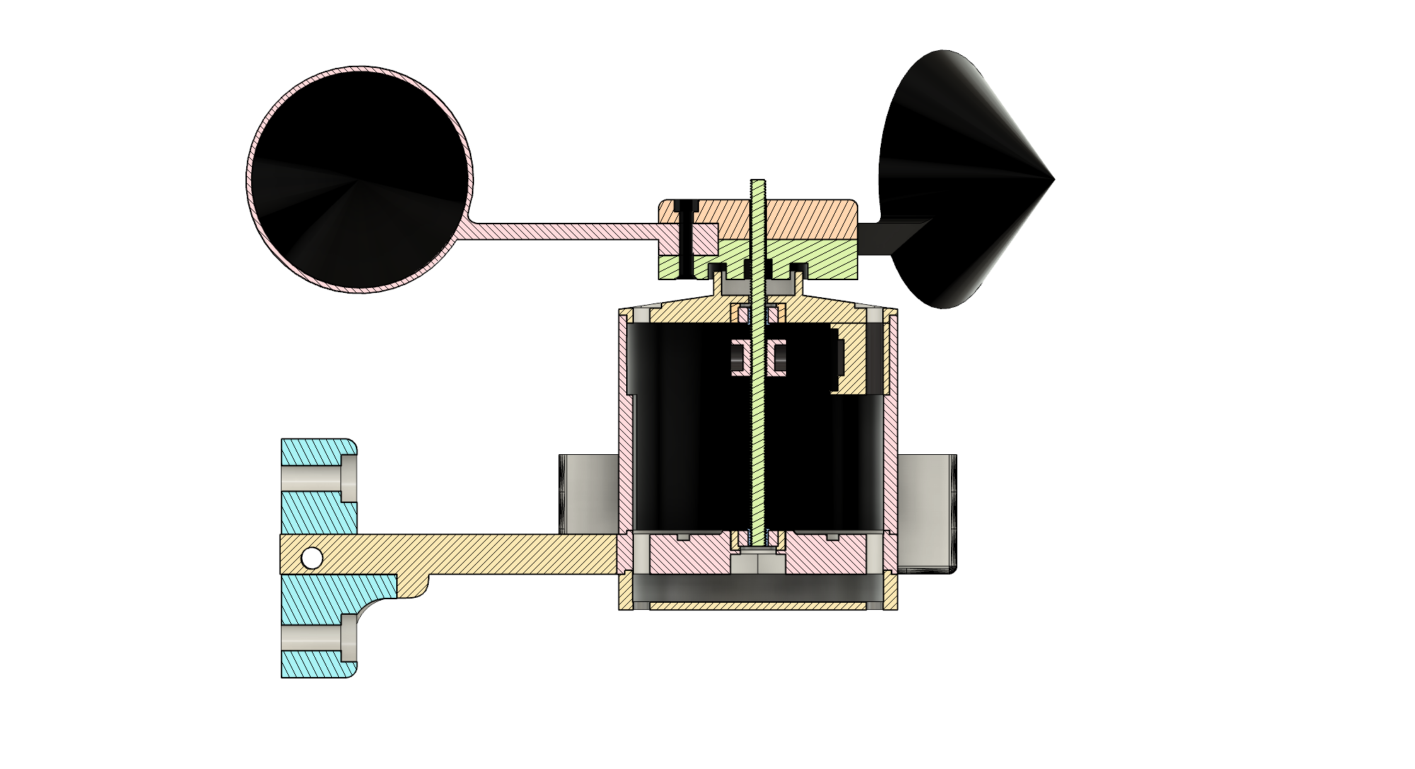
images/Anemometre+Girouette v535.png
