slash4you/Anemometre-Girouette/images/Anemometre+Girouette v535_2.png

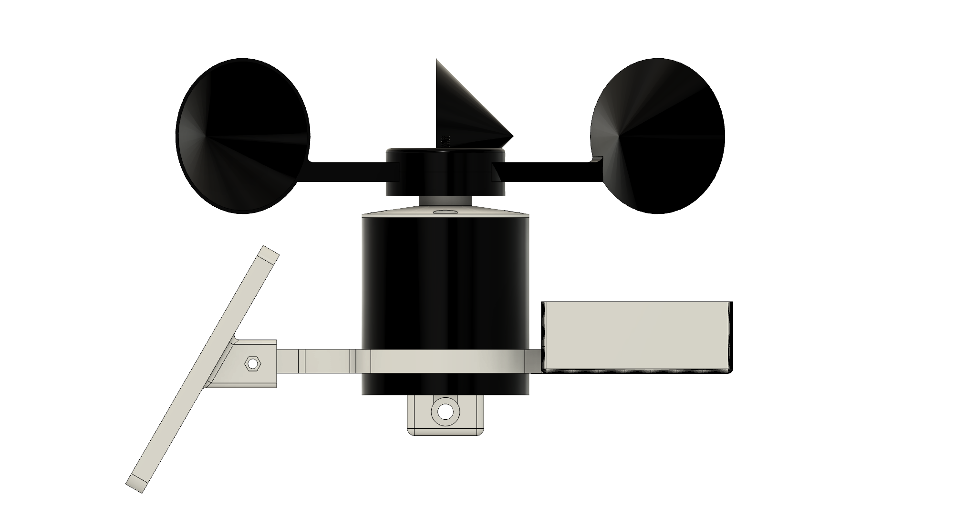
images/Anemometre+Girouette v535_2.png
