slash4you/Anemometre-Girouette/images/Anemometre+Girouette v535_3.png

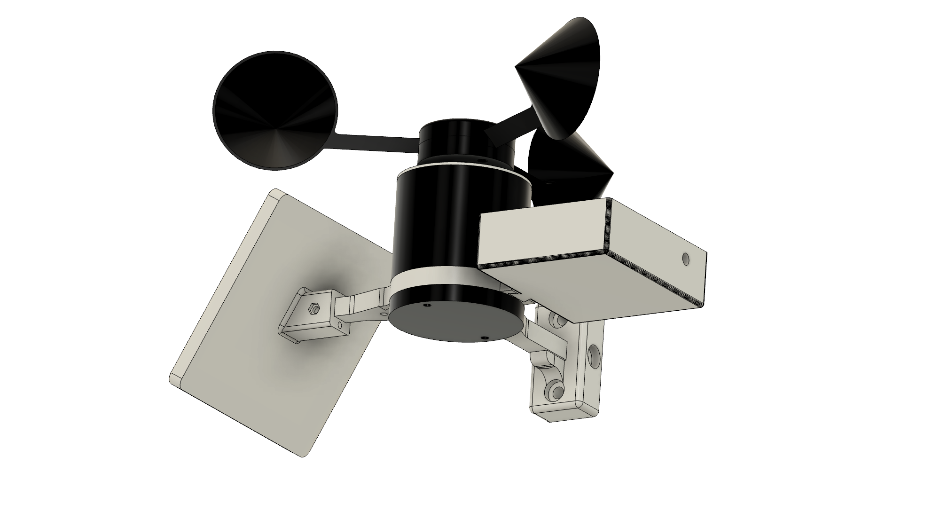
images/Anemometre+Girouette v535_3.png
