slash4you/Anemometre-Girouette/images/Anemometre+Girouette v535_4.jpeg

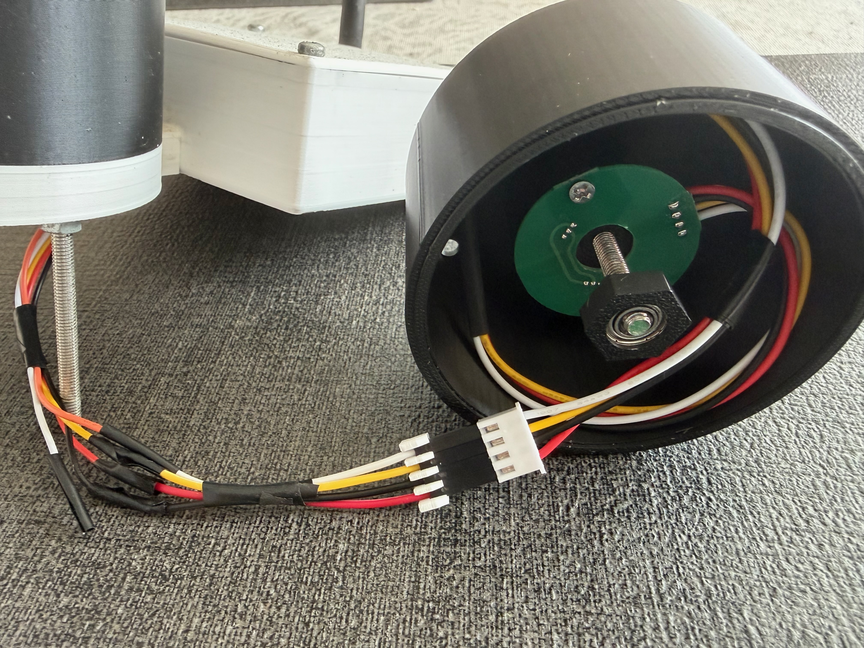
images/Anemometre+Girouette v535_4.jpeg
