slash4you/Anemometre-Girouette/images/Anemometre+Girouette v535_5.jpeg

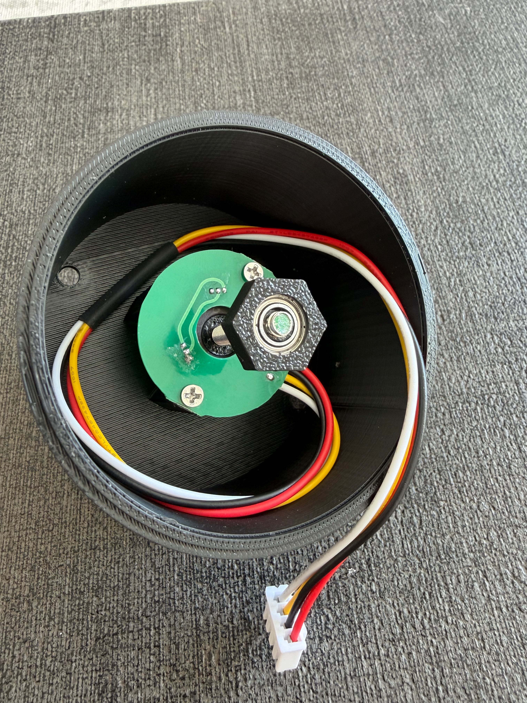
images/Anemometre+Girouette v535_5.jpeg
