slash4you/Anemometre-Girouette/images/Anemometre+Girouette v558.png

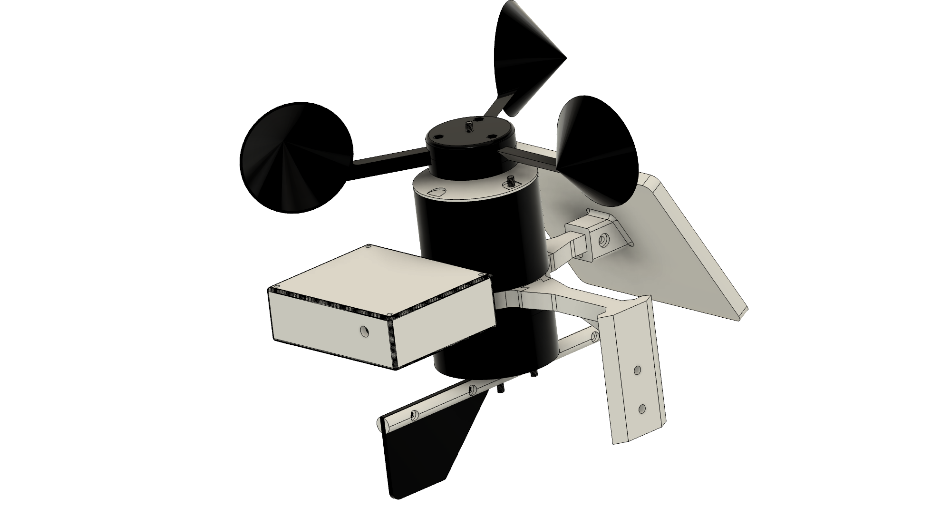
images/Anemometre+Girouette v558.png
