slash4you/Anemometre-Girouette/images/Anemometre+Girouette_1.jpeg

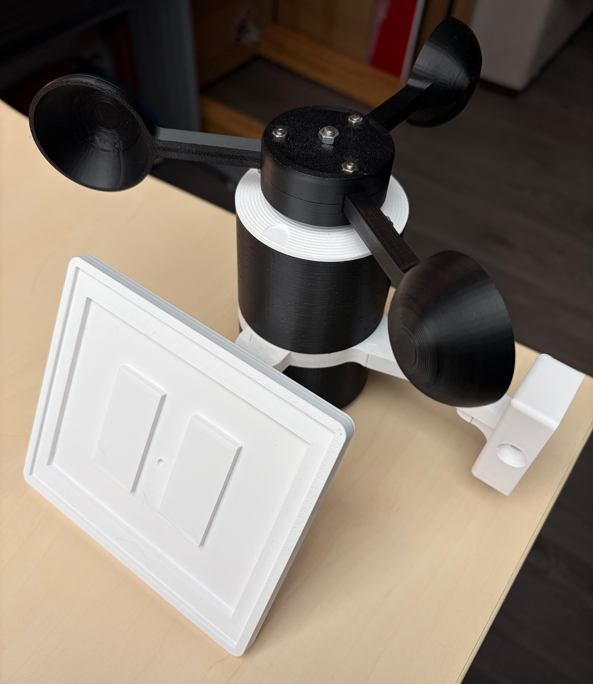
images/Anemometre+Girouette_1.jpeg
