slash4you/Anemometre-Girouette/images/Anemometre+Girouette_2.jpeg

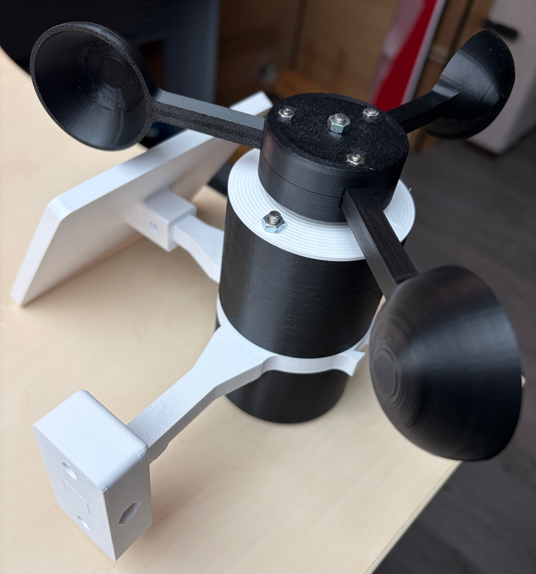
images/Anemometre+Girouette_2.jpeg
