slash4you/Anemometre-Girouette/images/Anemometre+Girouette_3.jpeg

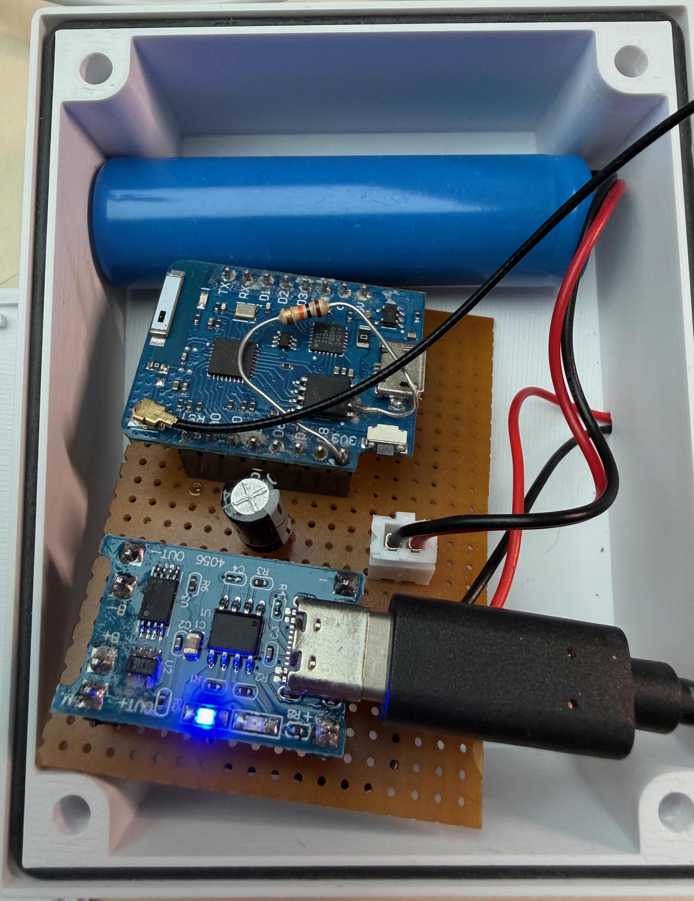
images/Anemometre+Girouette_3.jpeg
