slash4you/Anemometre-Girouette/images/Anemometre+Girouette_8.jpeg

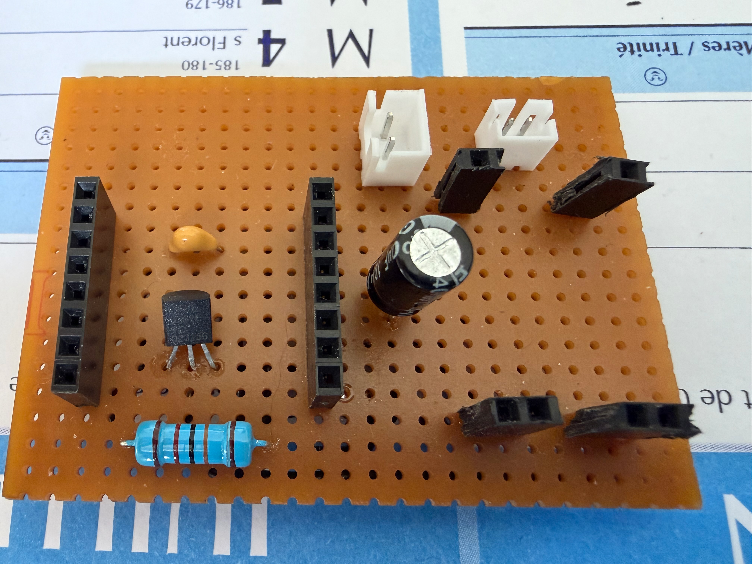
images/Anemometre+Girouette_8.jpeg
