slash4you/Anemometre-Girouette/images/Anemometre+Girouette_9.jpeg

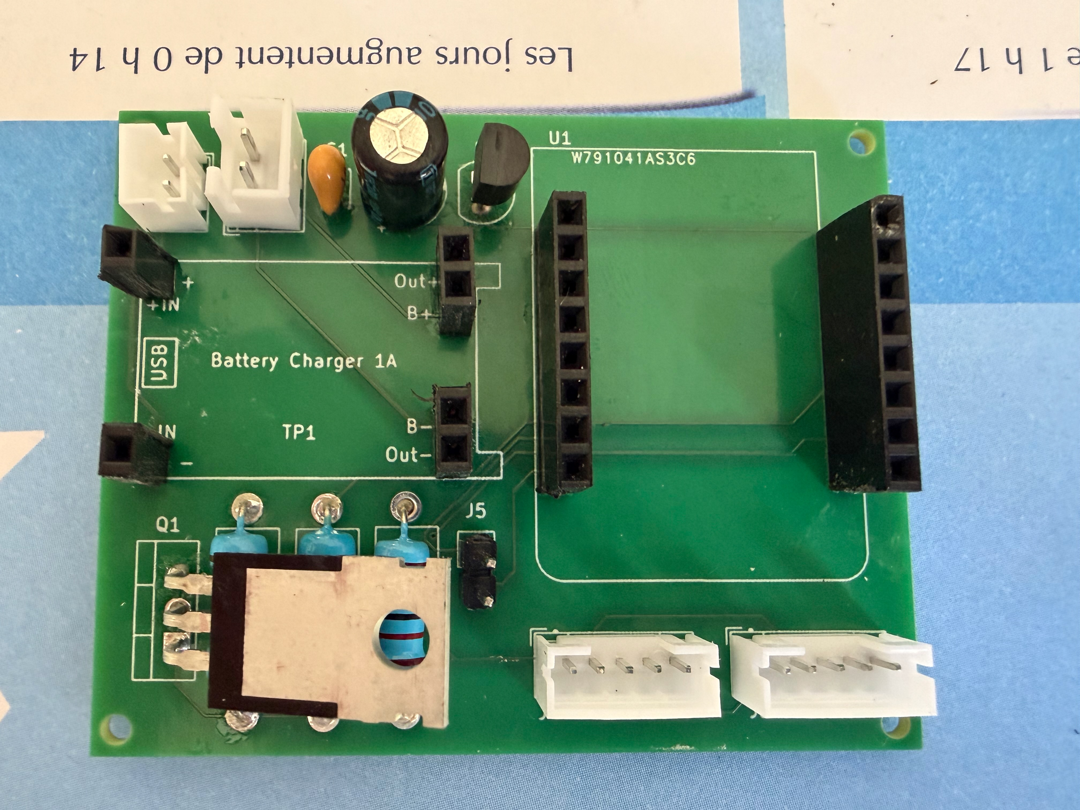
images/Anemometre+Girouette_9.jpeg
