slash4you/Anemometre-Girouette/images/Anemometre+Girouette_12.jpeg

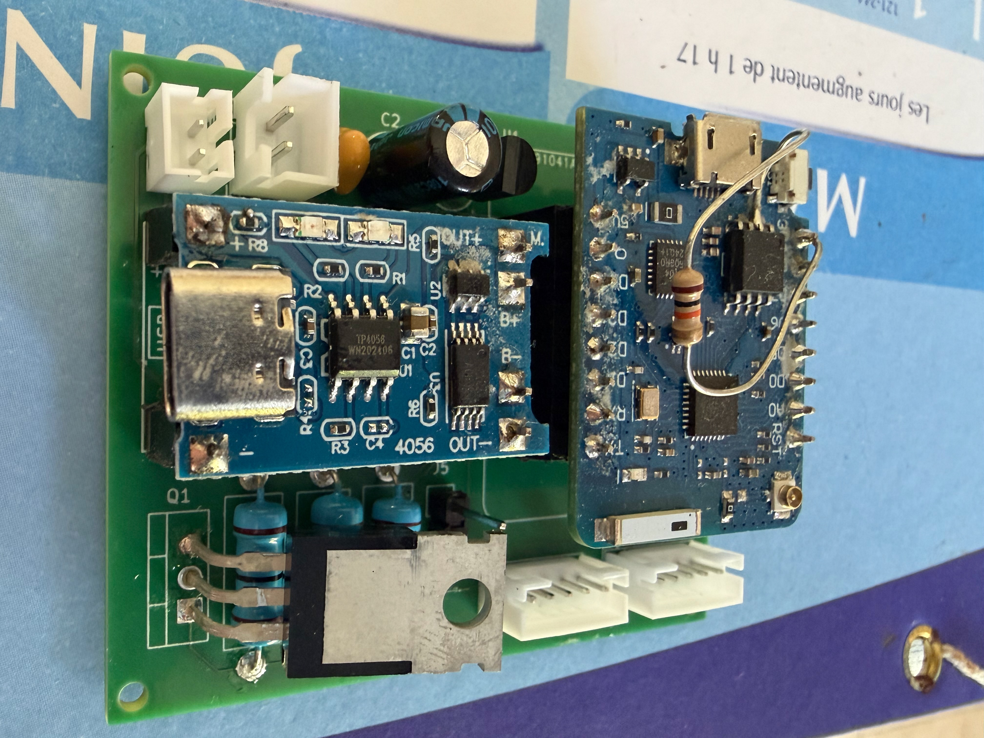
images/Anemometre+Girouette_12.jpeg
