slash4you/Anemometre-Girouette/images/Anemometre+Girouette_13.jpeg

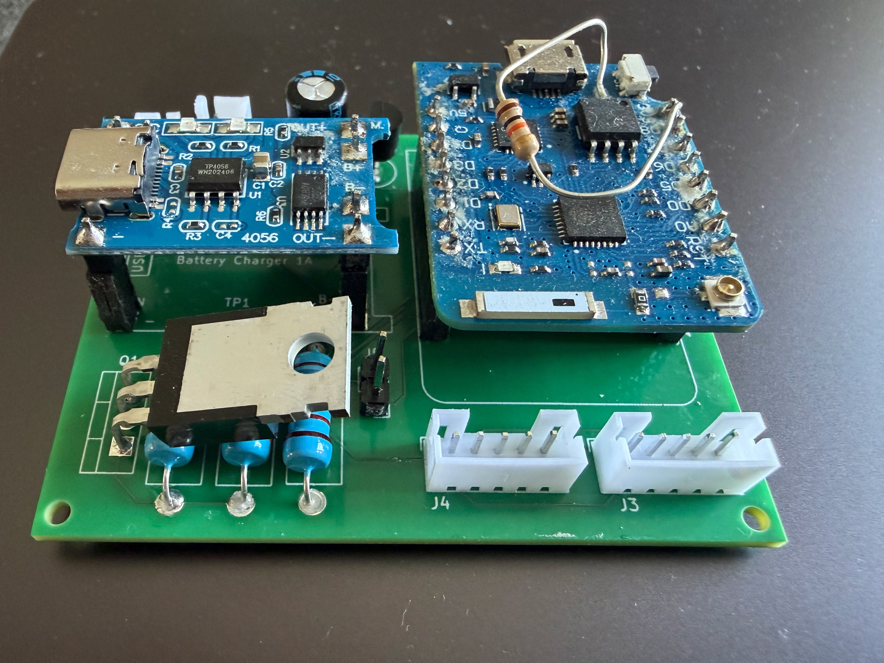
images/Anemometre+Girouette_13.jpeg
