slash4you/Anemometre-Girouette/images/Anemometre+Girouette_15.jpeg

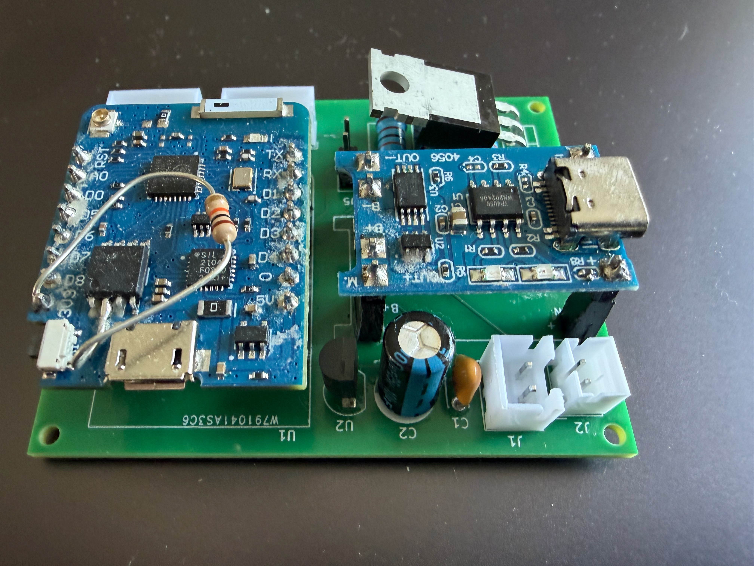
images/Anemometre+Girouette_15.jpeg
