slash4you/Anemometre-Girouette/images/Anemometre+Girouette_19.jpeg

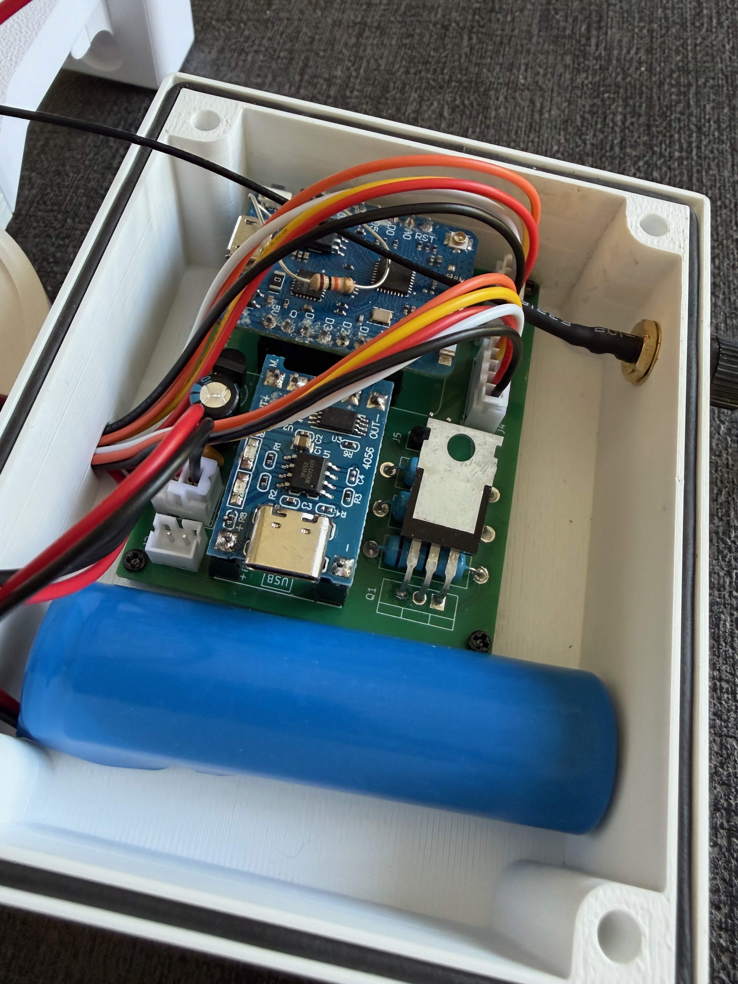
images/Anemometre+Girouette_19.jpeg
