slash4you/Anemometre-Girouette/images/Anemometre+Girouette_23.jpeg

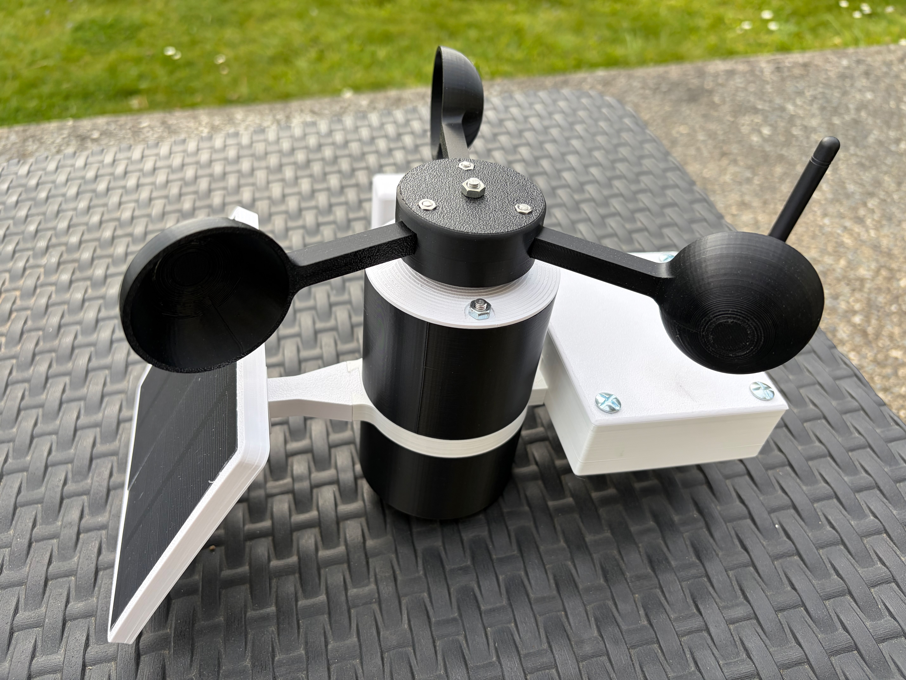
images/Anemometre+Girouette_23.jpeg
