slash4you/Anemometre-Girouette/images/Anemometre+Girouette_26.jpeg

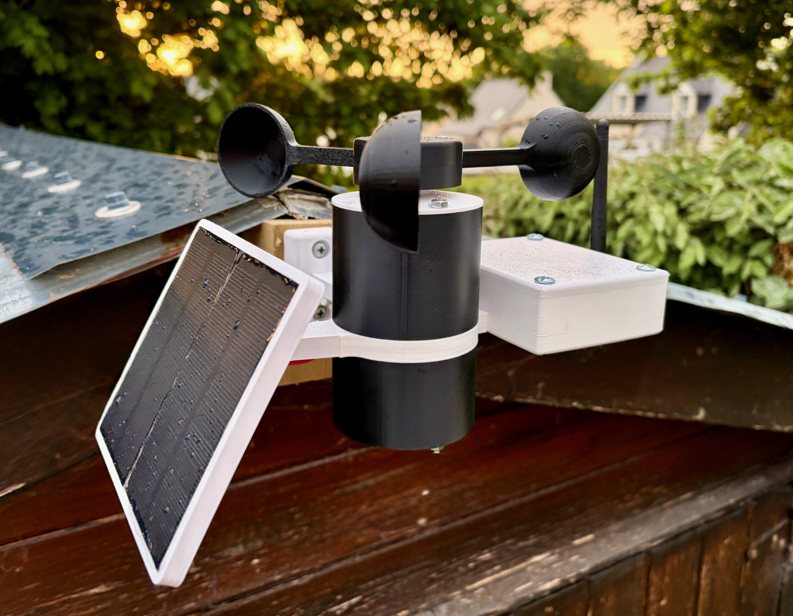
images/Anemometre+Girouette_26.jpeg
