slash4you/Anemometre-Girouette/images/Anemometre+Girouette_27.jpeg

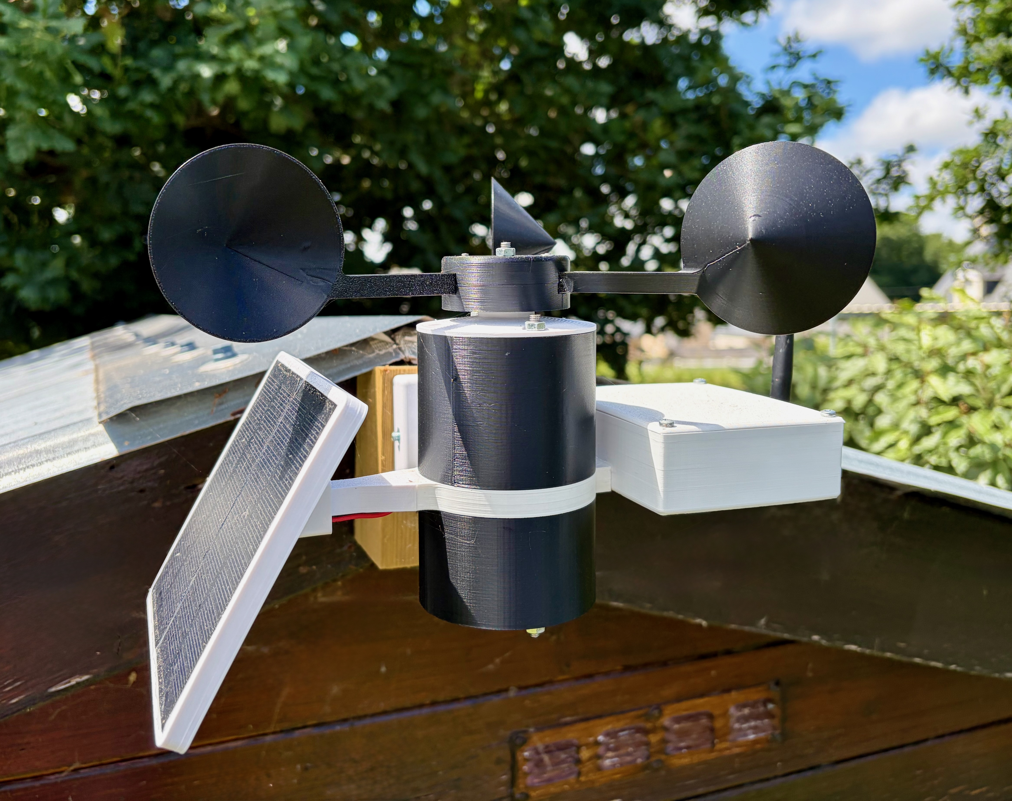
images/Anemometre+Girouette_27.jpeg
