slash4you/Anemometre-Girouette/images/Anemometre+Girouette_28.jpeg

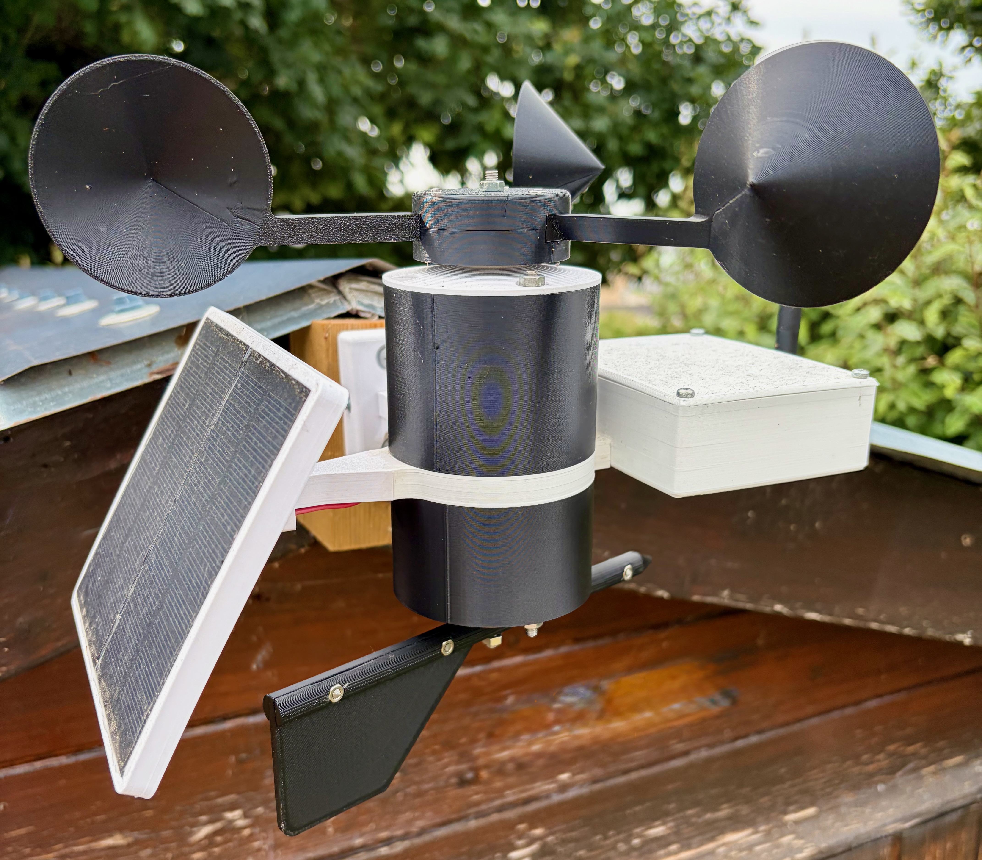
images/Anemometre+Girouette_28.jpeg
