slash4you/Anemometre-Girouette/images/Dashboard.HomeAssistant.jpeg

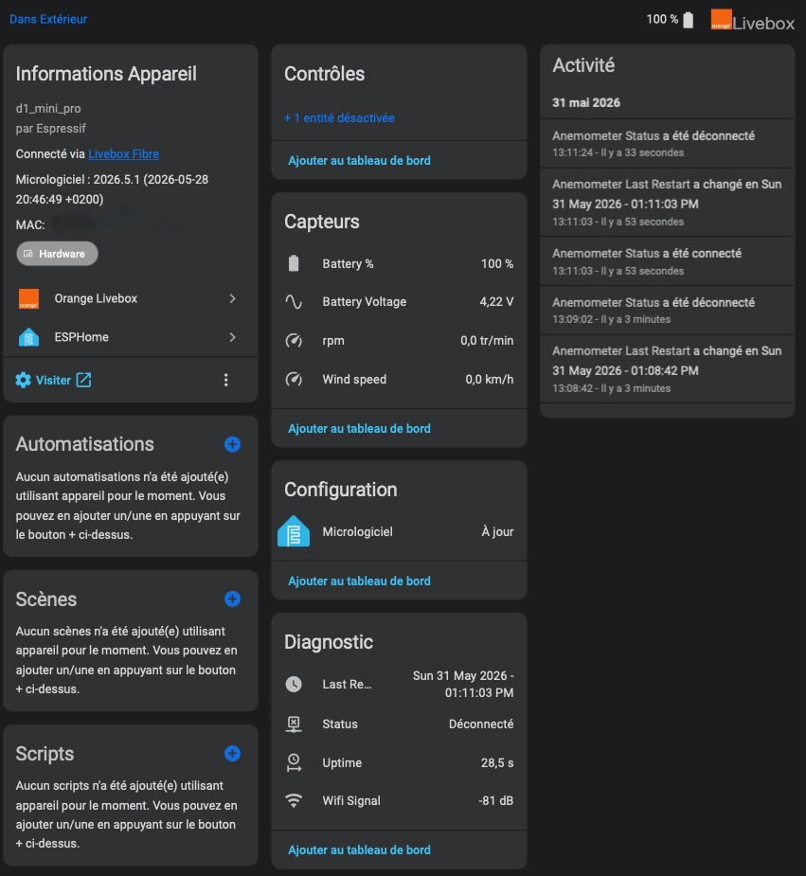
images/Dashboard.HomeAssistant.jpeg
