slash4you/Anemometre-Girouette/stl/Liaison Anémomètre.stl

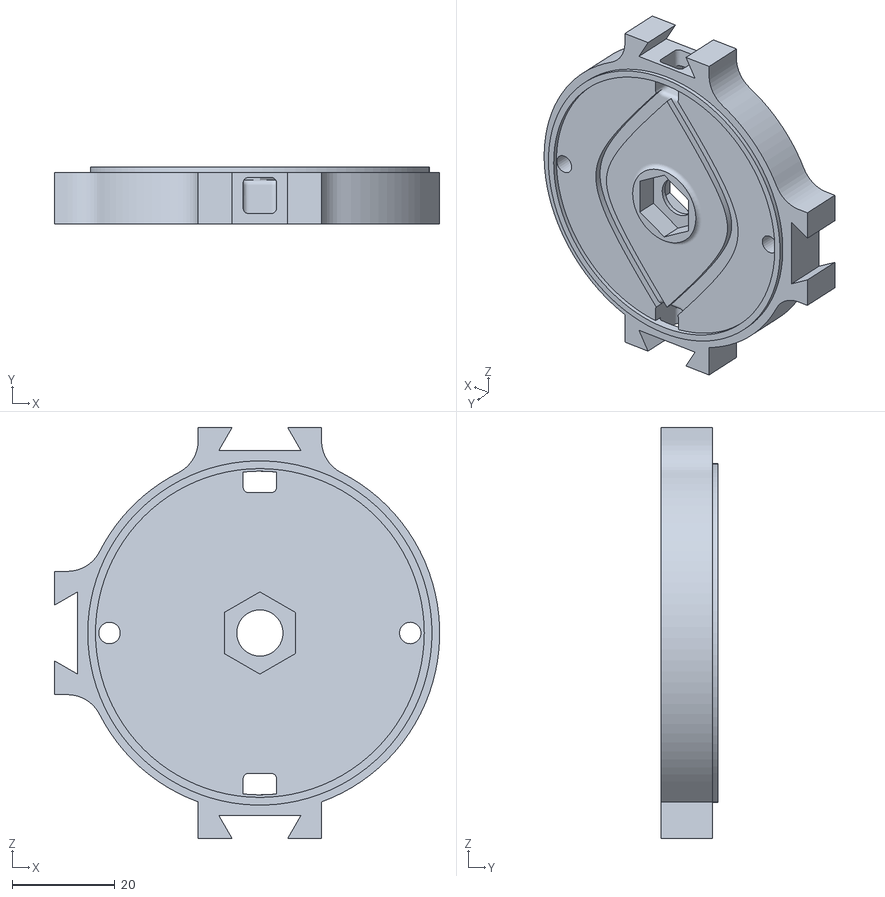
[picture p99: CAD file, 2026-04-24]
stl/Liaison Anémomètre.stl
75.0 x 11.0 x 80.0
