slash4you/Anemometre-Girouette/stl/Anemometre - boitier.stl

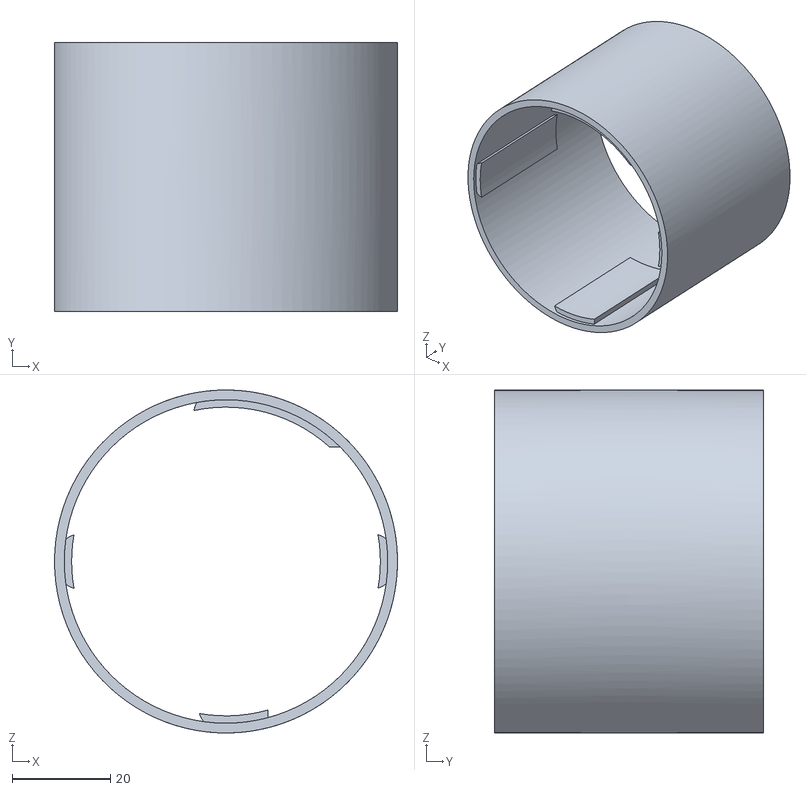
[picture p100: CAD file, 2026-03-15]
stl/Anemometre - boitier.stl
70.0 x 55.0 x 70.0
