slash4you/Anemometre-Girouette/stl/Anemometre - Support US1881.stl

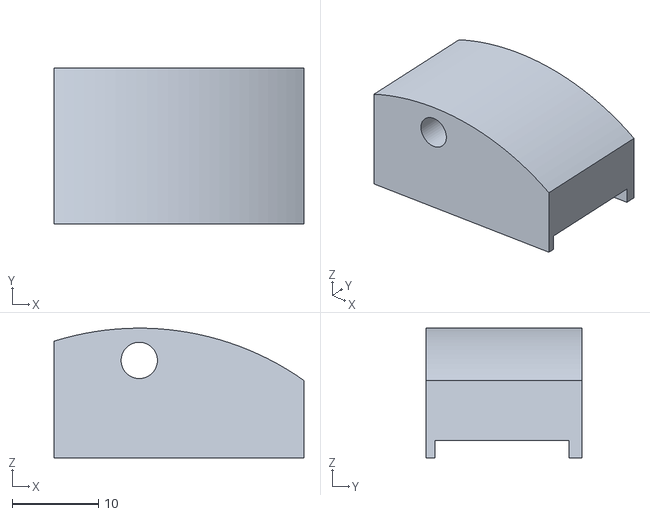
[picture p101: CAD file, 2026-03-15]
stl/Anemometre - Support US1881.stl
28.9 x 18.0 x 15.0
