slash4you/Anemometre-Girouette/stl/Anemometre - support aimants.stl

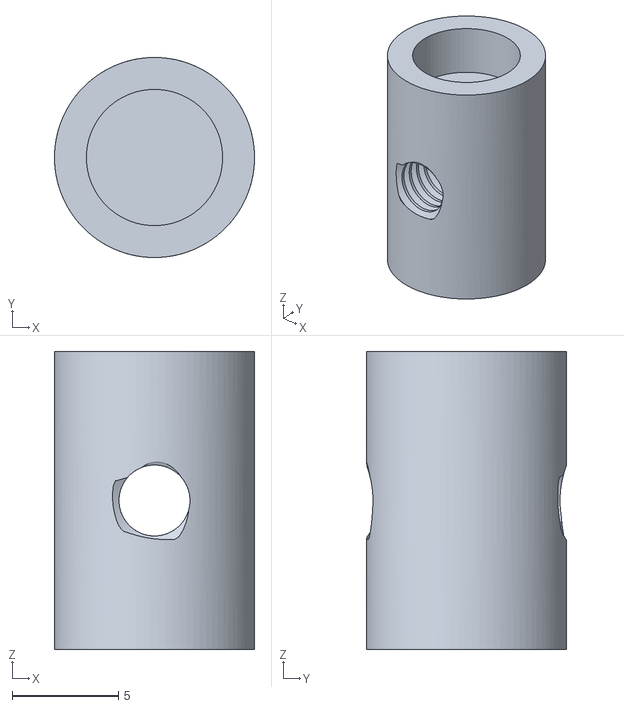
[picture p102: CAD file, 2026-03-14]
stl/Anemometre - support aimants.stl
9.40 x 9.40 x 14.0
