slash4you/Anemometre-Girouette/stl/Support Helice Inf.stl

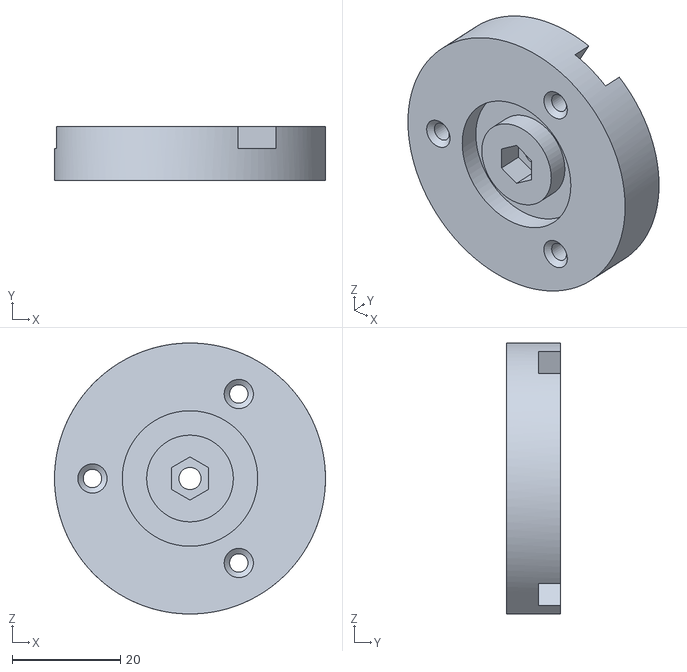
[picture p103: CAD file, 2026-02-22]
stl/Support Helice Inf.stl
50.0 x 10.0 x 50.0
