slash4you/Anemometre-Girouette/stl/Support Helice Sup.stl

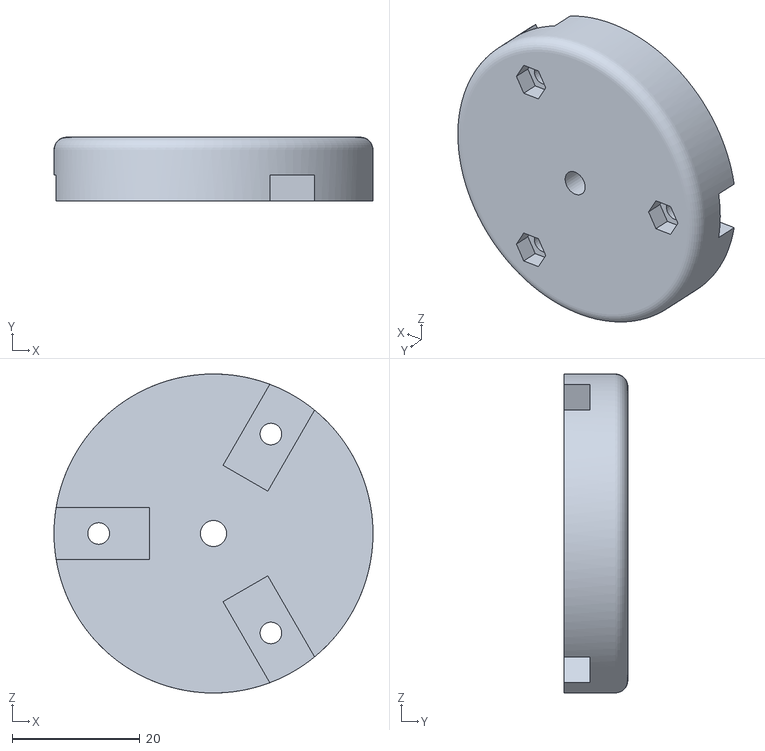
[picture p104: CAD file, 2026-02-22]
stl/Support Helice Sup.stl
50.0 x 10.0 x 50.0
