slash4you/Anemometre-Girouette/stl/Liaison Mur.stl

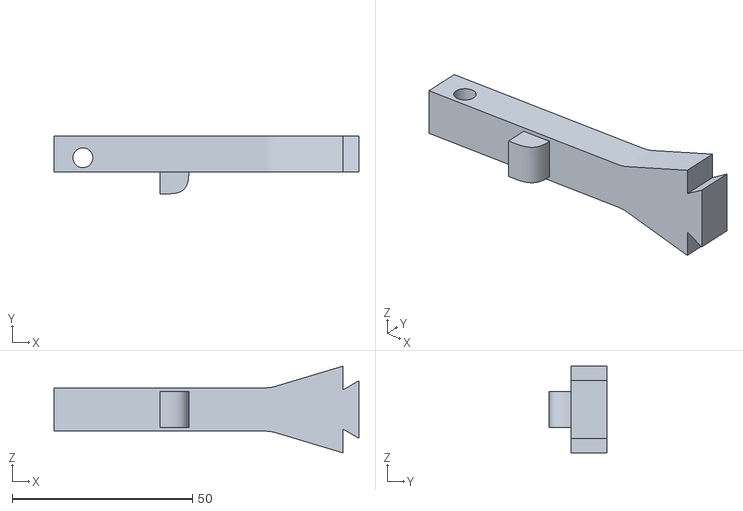
[picture p105: CAD file, 2026-02-20]
stl/Liaison Mur.stl
84.5 x 16.0 x 24.0
