slash4you/Anemometre-Girouette/stl/Girouette - Flèche.stl

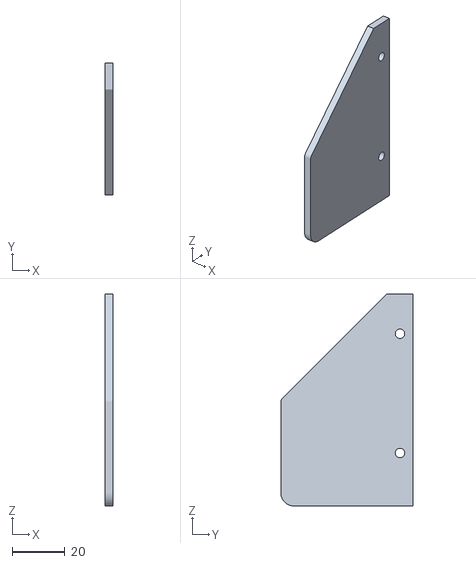
[picture p106: CAD file, 2026-02-20]
stl/Girouette - Flèche.stl
3.00 x 50.0 x 80.0
