slash4you/Anemometre-Girouette/stl/Panneau solaire double fixe.stl

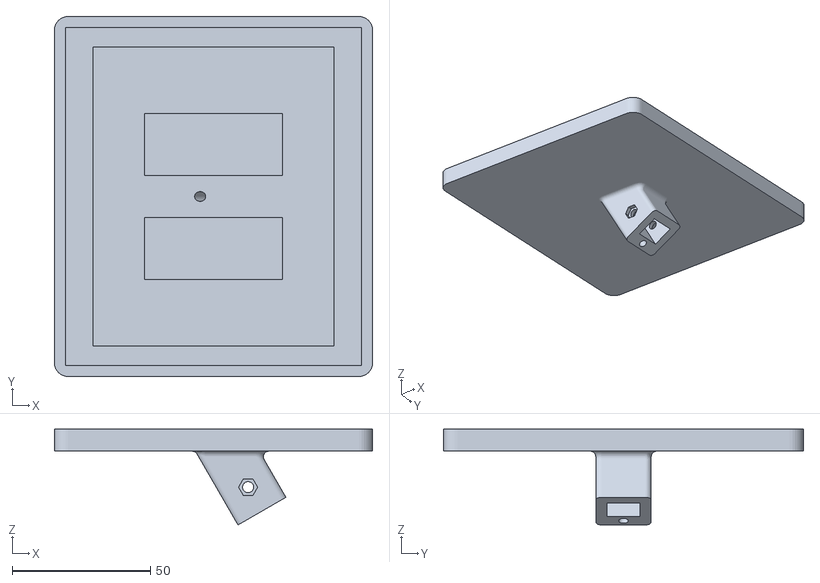
[picture p107: CAD file, 2026-02-20]
stl/Panneau solaire double fixe.stl
115.0 x 130.0 x 34.7
