slash4you/Anemometre-Girouette/stl/Anemometre - Axe Etalon.stl

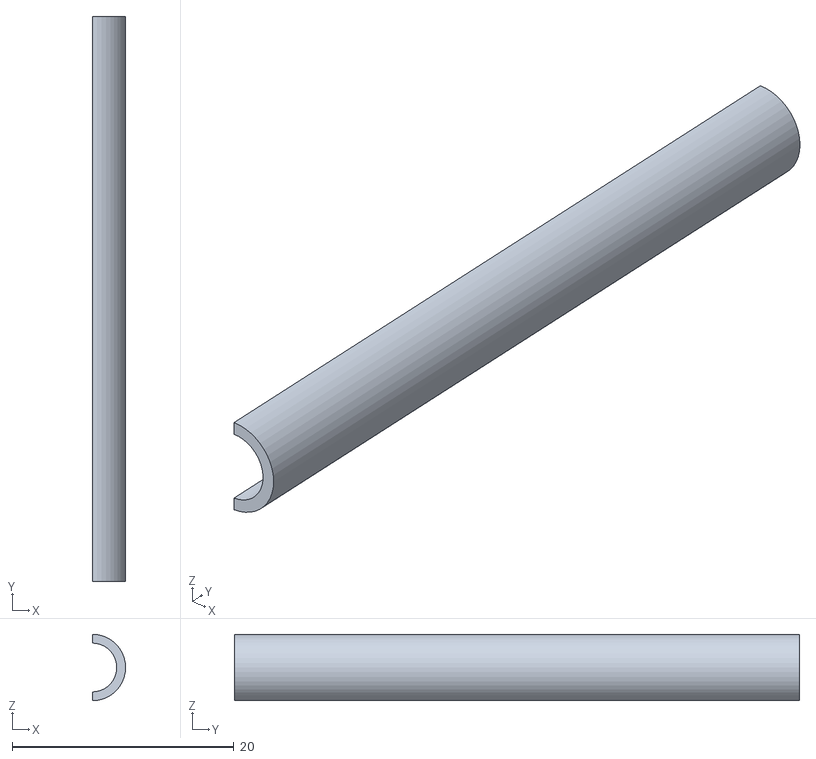
[picture p108: CAD file, 2026-02-20]
stl/Anemometre - Axe Etalon.stl
3.00 x 51.0 x 6.00
