slash4you/Anemometre-Girouette/stl/Anemometre - Couvercle Sup.stl

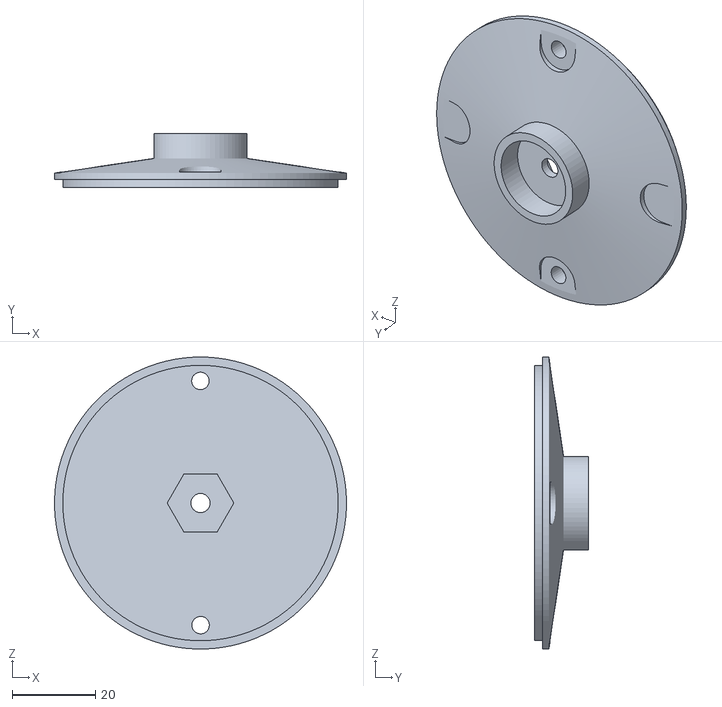
[picture p109: CAD file, 2026-02-20]
stl/Anemometre - Couvercle Sup.stl
70.0 x 13.0 x 70.0
