slash4you/Anemometre-Girouette/stl/Helice.stl

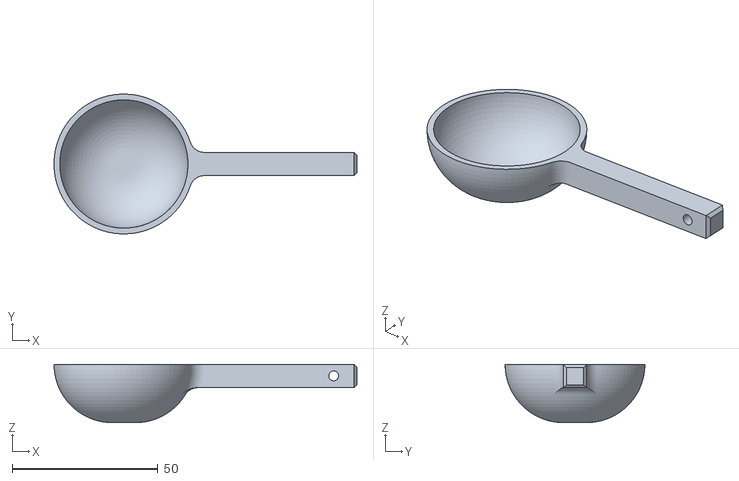
[picture p110: CAD file, 2026-02-20]
stl/Helice.stl
104.0 x 48.0 x 20.0
