slash4you/Anemometre-Girouette/stl/Fixation murale.stl

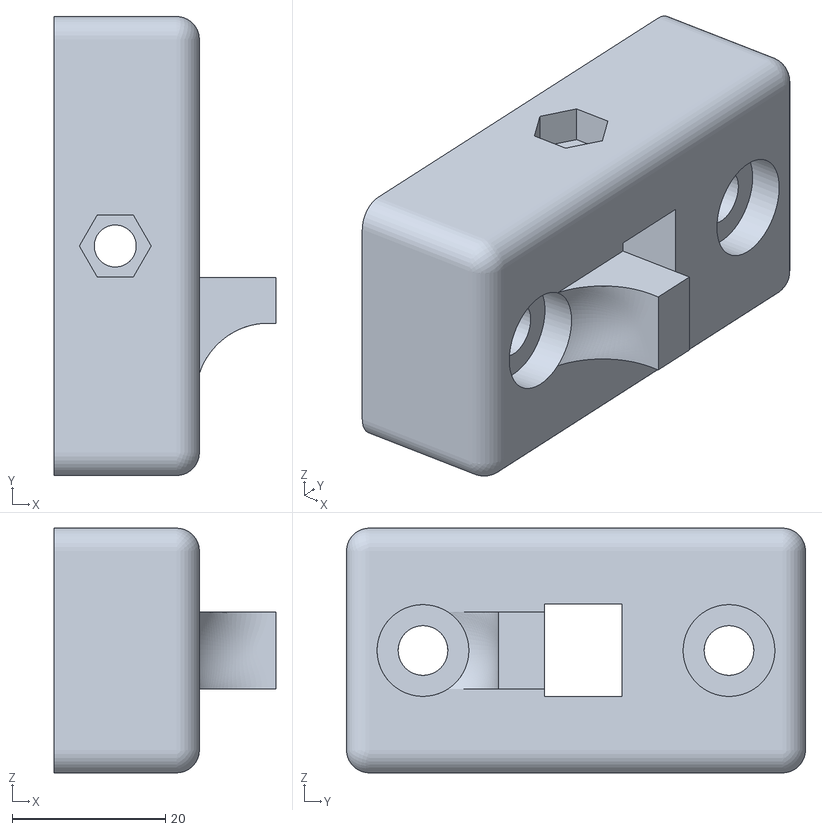
[picture p111: CAD file, 2026-02-20]
stl/Fixation murale.stl
29.0 x 60.0 x 32.0
