slash4you/Anemometre-Girouette/stl/Girouette - Axe Etalon.stl

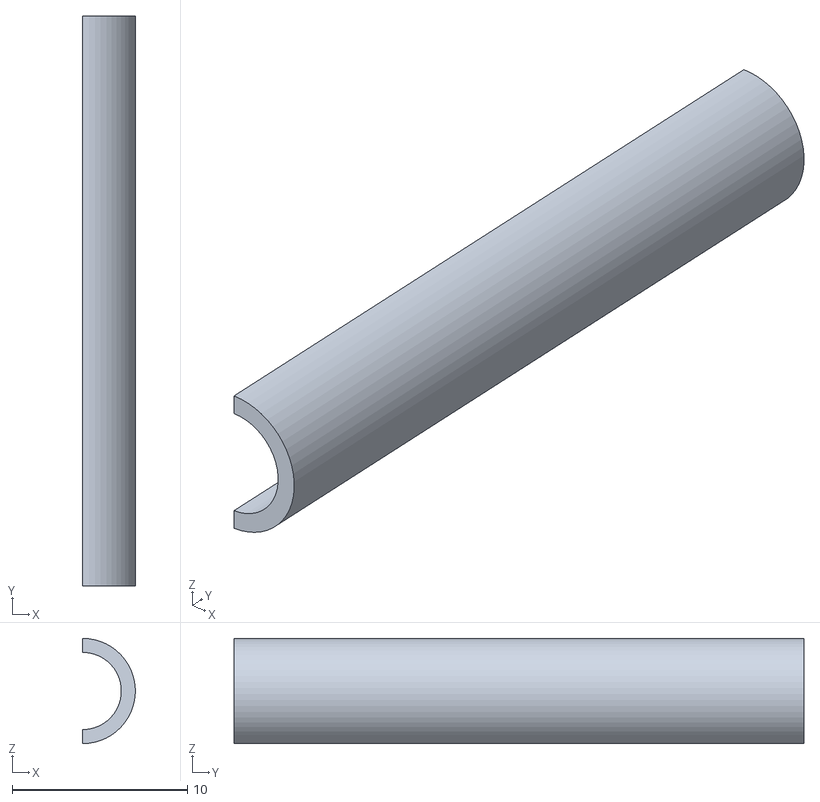
[picture p112: CAD file, 2026-02-20]
stl/Girouette - Axe Etalon.stl
2.99 x 32.5 x 6.00
