slash4you/Anemometre-Girouette/stl/Roulement.stl

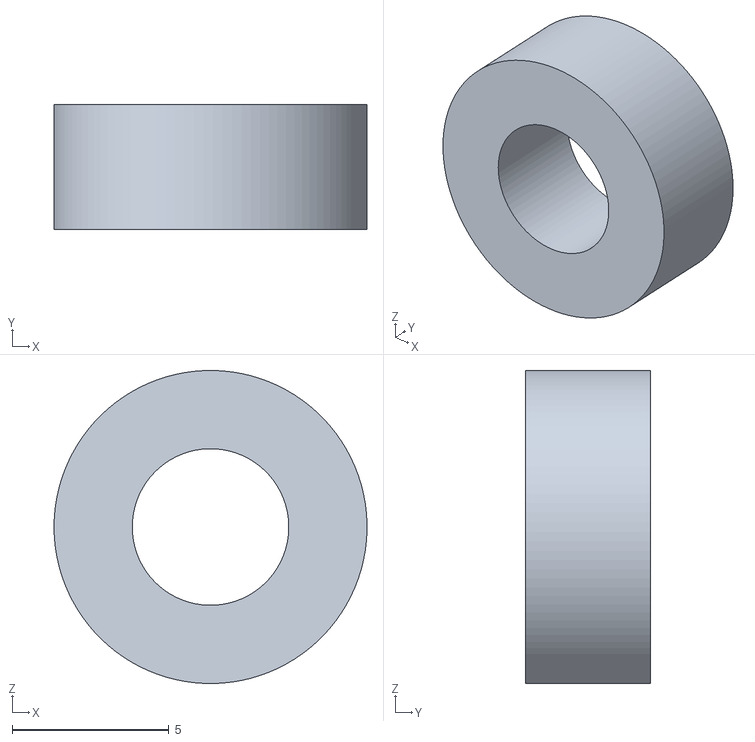
[picture p113: CAD file, 2026-02-20]
stl/Roulement.stl
10.00 x 4.00 x 10.00
