slash4you/Anemometre-Girouette/stl/Cage roulement.stl

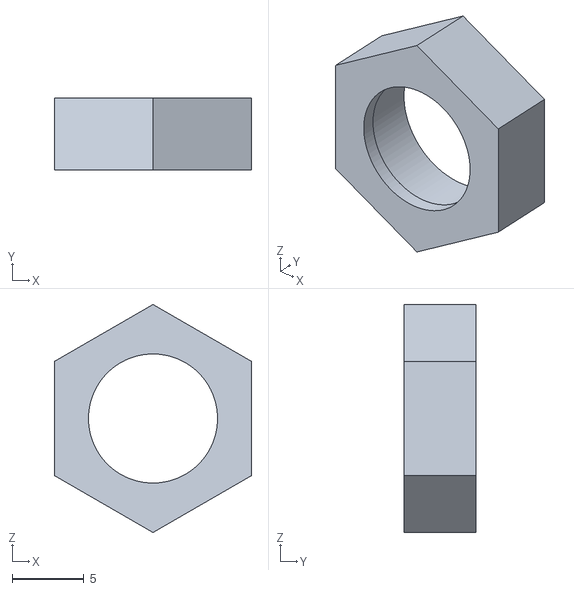
[picture p114: CAD file, 2026-02-20]
stl/Cage roulement.stl
13.8 x 5.00 x 15.9
